cyrillvalentini/SAP-Extended/schematics/SAP-Extended/A-Register.kicad_sch

## KiCad design schematics/SAP-Extended/A-Register.kicad_sch (2023-11-03)

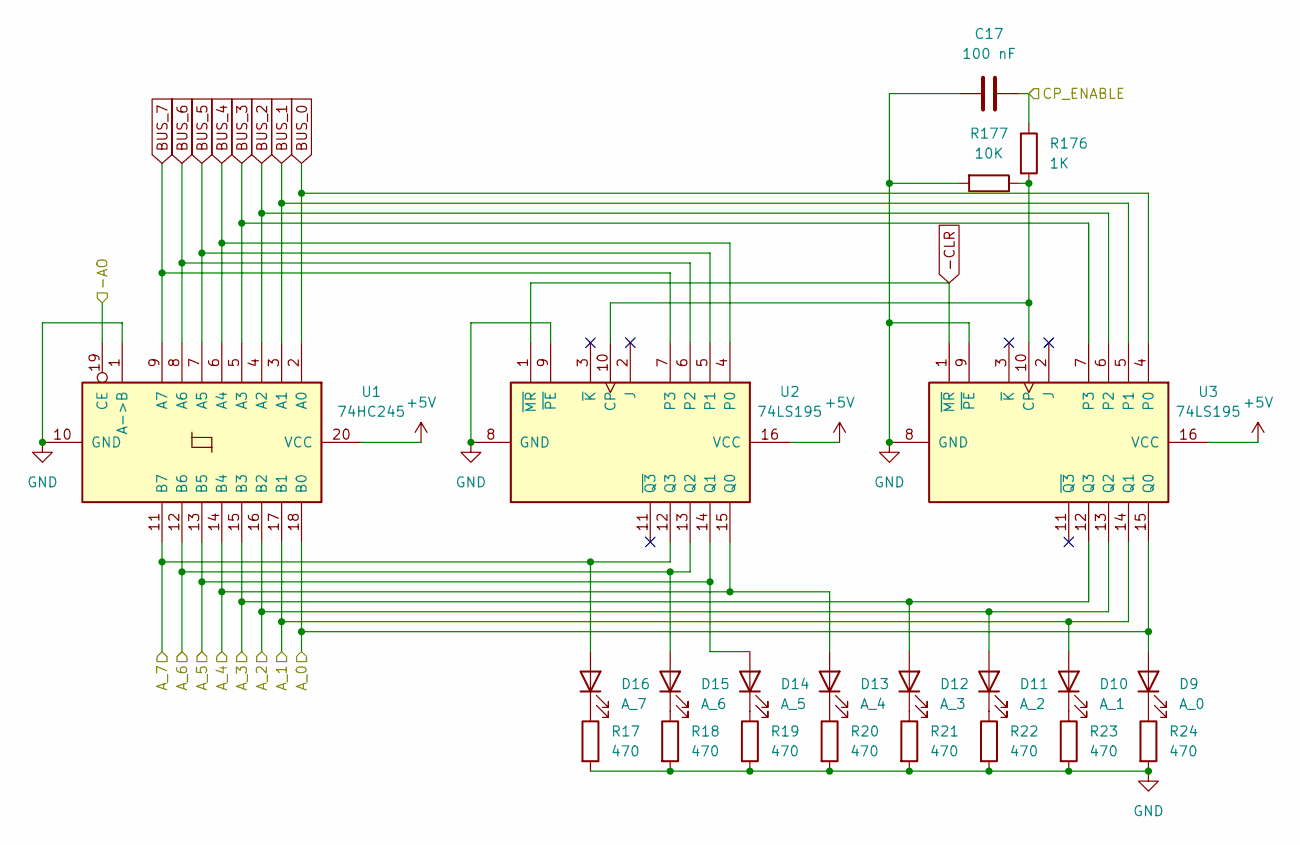
[picture p16: schematic A-Register.kicad_sch]

Parts:
C17: 100 nF; R_1206_3216Metric_Pad1.30x1.75mm_HandSolder
D9: A_0; LED_D3.0mm
D10: A_1; LED_D3.0mm
D11: A_2; LED_D3.0mm
D12: A_3; LED_D3.0mm
D13: A_4; LED_D3.0mm
D14: A_5; LED_D3.0mm
D15: A_6; LED_D3.0mm
D16: A_7; LED_D3.0mm
R17, R18, R19, R20, R21, R22, R23, R24: 470; R_1206_3216Metric_Pad1.30x1.75mm_HandSolder
R176: 1K; R_1206_3216Metric_Pad1.30x1.75mm_HandSolder
R177: 10K; R_1206_3216Metric_Pad1.30x1.75mm_HandSolder
U1: 74HC245; DIP-20_W7.62mm_Socket
U2, U3: 74LS195; DIP-16_W7.62mm_Socket

Connections:
+5V: U1.20 (VCC), U2.16 (VCC), U3.16 (VCC)
-AO: U1.19 (CE)
-CLR: U2.1 (~MR), U3.1 (~MR)
A_0: D9.2 (A), U1.18 (B0), U3.15 (Q0)
A_1: D10.2 (A), U1.17 (B1), U3.14 (Q1)
A_2: D11.2 (A), U1.16 (B2), U3.13 (Q2)
A_3: D12.2 (A), U1.15 (B3), U3.12 (Q3)
A_4: D13.2 (A), U1.14 (B4), U2.15 (Q0)
A_5: D14.2 (A), U1.13 (B5), U2.14 (Q1)
A_6: D15.2 (A), U1.12 (B6), U2.13 (Q2)
A_7: D16.2 (A), U1.11 (B7), U2.12 (Q3)
BUS_0: U1.2 (A0), U3.4 (P0)
BUS_1: U1.3 (A1), U3.5 (P1)
BUS_2: U1.4 (A2), U3.6 (P2)
BUS_3: U1.5 (A3), U3.7 (P3)
BUS_4: U1.6 (A4), U2.4 (P0)
BUS_5: U1.7 (A5), U2.5 (P1)
BUS_6: U1.8 (A6), U2.6 (P2)
BUS_7: U1.9 (A7), U2.7 (P3)
CP_ENABLE: C17.1, R176.1
GND: C17.2, R17.2, R18.2, R19.2, R20.2, R21.2, R22.2, R23.2, R24.2, R177.2, U1.1 (A->B), U1.10 (GND), U2.8 (GND), U2.9 (~PE), U3.8 (GND), U3.9 (~PE)
unnamed: D9.1 (K), R24.1
unnamed: D10.1 (K), R23.1
unnamed: D11.1 (K), R22.1
unnamed: D12.1 (K), R21.1
unnamed: D13.1 (K), R20.1
unnamed: D14.1 (K), R19.1
unnamed: D15.1 (K), R18.1
unnamed: D16.1 (K), R17.1
unnamed: R176.2, R177.1, U2.10 (CP), U3.10 (CP)
