cyrillvalentini/SAP-Extended/schematics/SAP-Extended/ALU.kicad_sch

## KiCad design schematics/SAP-Extended/ALU.kicad_sch (2023-11-03)

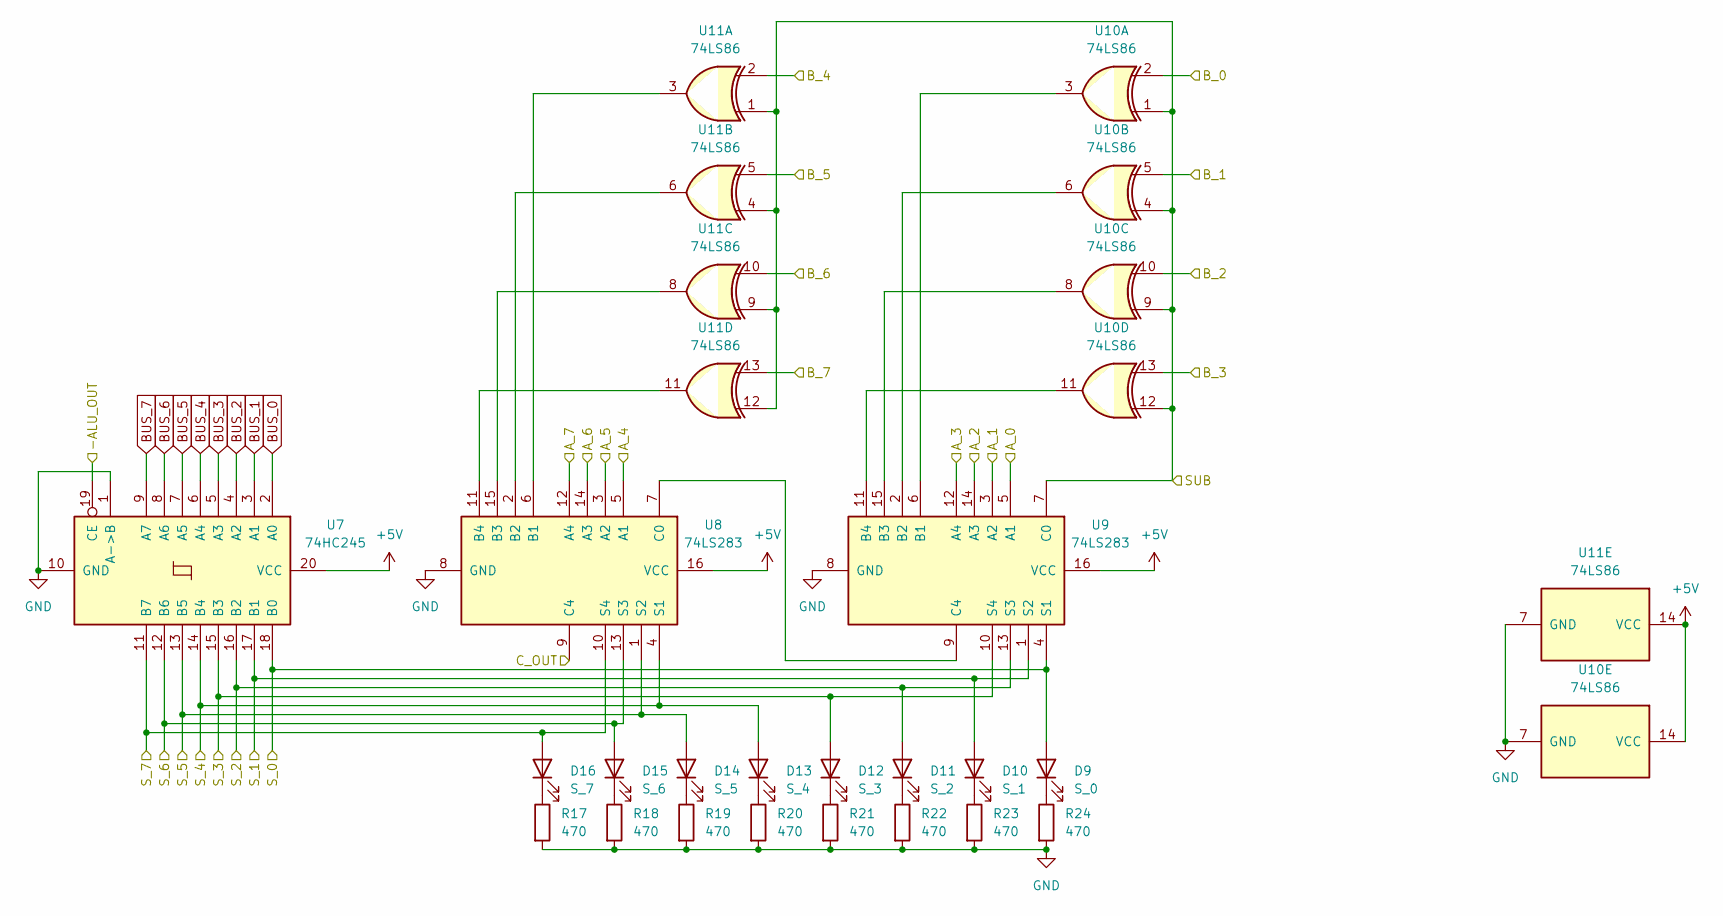
[picture p17: schematic ALU.kicad_sch]

Parts:
D9: S_0; LED_D3.0mm
D10: S_1; LED_D3.0mm
D11: S_2; LED_D3.0mm
D12: S_3; LED_D3.0mm
D13: S_4; LED_D3.0mm
D14: S_5; LED_D3.0mm
D15: S_6; LED_D3.0mm
D16: S_7; LED_D3.0mm
R17, R18, R19, R20, R21, R22, R23, R24: 470; R_1206_3216Metric_Pad1.30x1.75mm_HandSolder
U7: 74HC245; DIP-20_W7.62mm_Socket
U8, U9: 74LS283; DIP-16_W7.62mm_Socket
U10, U11: 74LS86; DIP-14_W7.62mm_Socket

Connections:
+5V: U7.20 (VCC), U8.16 (VCC), U9.16 (VCC), U10.14 (VCC), U11.14 (VCC)
-ALU_OUT: U7.19 (CE)
A_0: U9.5 (A1)
A_1: U9.3 (A2)
A_2: U9.14 (A3)
A_3: U9.12 (A4)
A_4: U8.5 (A1)
A_5: U8.3 (A2)
A_6: U8.14 (A3)
A_7: U8.12 (A4)
BUS_0: U7.2 (A0)
BUS_1: U7.3 (A1)
BUS_2: U7.4 (A2)
BUS_3: U7.5 (A3)
BUS_4: U7.6 (A4)
BUS_5: U7.7 (A5)
BUS_6: U7.8 (A6)
BUS_7: U7.9 (A7)
B_0: U10.2
B_1: U10.5
B_2: U10.10
B_3: U10.13
B_4: U11.2
B_5: U11.5
B_6: U11.10
B_7: U11.13
C_OUT: U8.9 (C4)
GND: R17.2, R18.2, R19.2, R20.2, R21.2, R22.2, R23.2, R24.2, U7.1 (A->B), U7.10 (GND), U8.8 (GND), U9.8 (GND), U10.7 (GND), U11.7 (GND)
unnamed: D9.1 (K), R24.1
unnamed: D10.1 (K), R23.1
unnamed: D11.1 (K), R22.1
unnamed: D12.1 (K), R21.1
unnamed: D13.1 (K), R20.1
unnamed: D14.1 (K), R19.1
unnamed: D15.1 (K), R18.1
unnamed: D16.1 (K), R17.1
unnamed: U8.7 (C0), U9.9 (C4)
unnamed: U9.6 (B1), U10.3
unnamed: U9.2 (B2), U10.6
unnamed: U9.15 (B3), U10.8
unnamed: U9.11 (B4), U10.11
unnamed: U8.6 (B1), U11.3
unnamed: U8.2 (B2), U11.6
unnamed: U8.15 (B3), U11.8
unnamed: U8.11 (B4), U11.11
SUB: U9.7 (C0), U10.1, U10.4, U10.9, U10.12, U11.1, U11.4, U11.9, U11.12
S_0: D9.2 (A), U7.18 (B0), U9.4 (S1)
S_1: D10.2 (A), U7.17 (B1), U9.1 (S2)
S_2: D11.2 (A), U7.16 (B2), U9.13 (S3)
S_3: D12.2 (A), U7.15 (B3), U9.10 (S4)
S_4: D13.2 (A), U7.14 (B4), U8.4 (S1)
S_5: D14.2 (A), U7.13 (B5), U8.1 (S2)
S_6: D15.2 (A), U7.12 (B6), U8.13 (S3)
S_7: D16.2 (A), U7.11 (B7), U8.10 (S4)
