cyrillvalentini/SAP-Extended/schematics/SAP-Extended/B-Register.kicad_sch

## KiCad design schematics/SAP-Extended/B-Register.kicad_sch (2023-11-03)

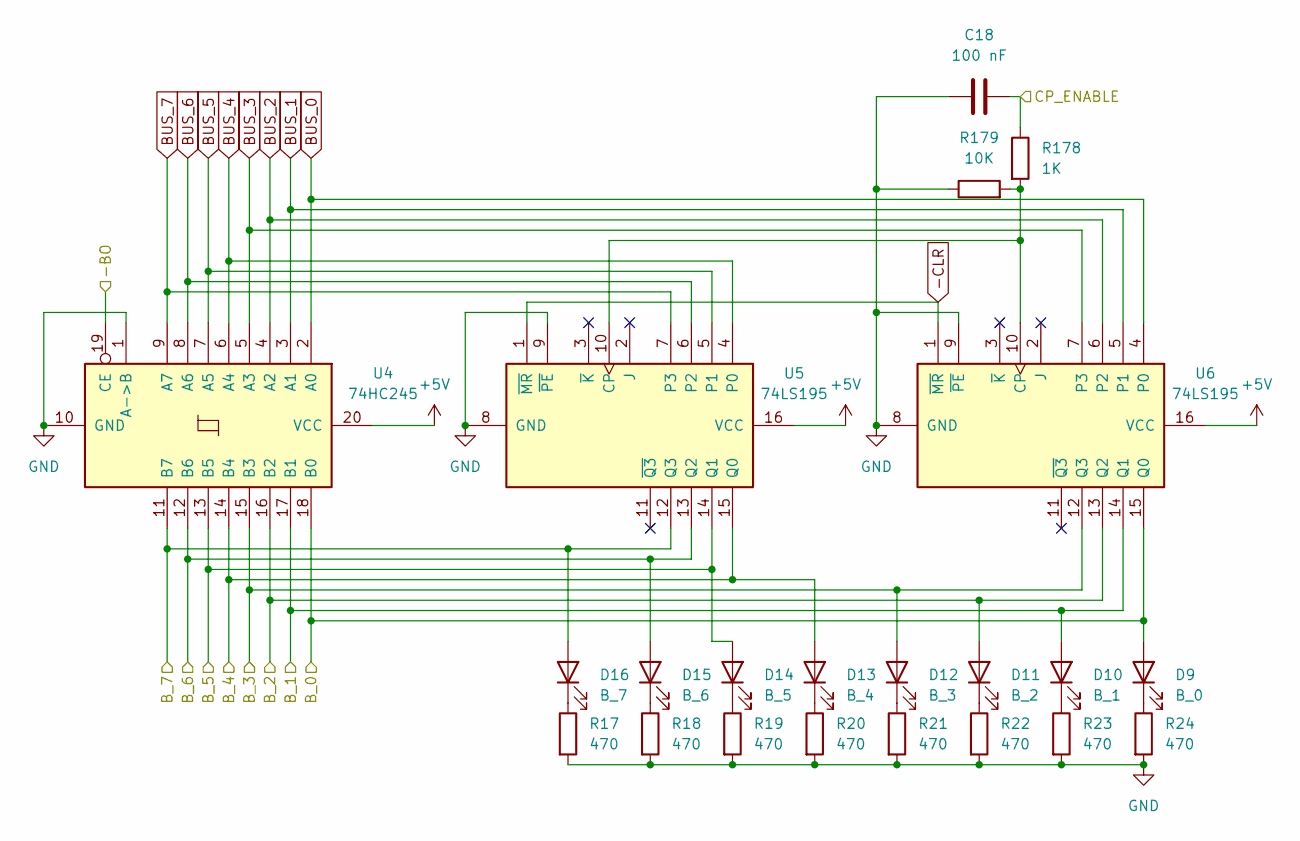
[picture p18: schematic B-Register.kicad_sch]

Parts:
C18: 100 nF
D9: B_0; LED_D3.0mm
D10: B_1; LED_D3.0mm
D11: B_2; LED_D3.0mm
D12: B_3; LED_D3.0mm
D13: B_4; LED_D3.0mm
D14: B_5; LED_D3.0mm
D15: B_6; LED_D3.0mm
D16: B_7; LED_D3.0mm
R17, R18, R19, R20, R21, R22, R23, R24: 470; R_1206_3216Metric_Pad1.30x1.75mm_HandSolder
R178: 1K; R_1206_3216Metric_Pad1.30x1.75mm_HandSolder
R179: 10K; R_1206_3216Metric_Pad1.30x1.75mm_HandSolder
U4: 74HC245; DIP-20_W7.62mm_Socket
U5, U6: 74LS195; DIP-16_W7.62mm_Socket

Connections:
+5V: U4.20 (VCC), U5.16 (VCC), U6.16 (VCC)
-BO: U4.19 (CE)
-CLR: U5.1 (~MR), U6.1 (~MR)
BUS_0: U4.2 (A0), U6.4 (P0)
BUS_1: U4.3 (A1), U6.5 (P1)
BUS_2: U4.4 (A2), U6.6 (P2)
BUS_3: U4.5 (A3), U6.7 (P3)
BUS_4: U4.6 (A4), U5.4 (P0)
BUS_5: U4.7 (A5), U5.5 (P1)
BUS_6: U4.8 (A6), U5.6 (P2)
BUS_7: U4.9 (A7), U5.7 (P3)
B_0: D9.2 (A), U4.18 (B0), U6.15 (Q0)
B_1: D10.2 (A), U4.17 (B1), U6.14 (Q1)
B_2: D11.2 (A), U4.16 (B2), U6.13 (Q2)
B_3: D12.2 (A), U4.15 (B3), U6.12 (Q3)
B_4: D13.2 (A), U4.14 (B4), U5.15 (Q0)
B_5: D14.2 (A), U4.13 (B5), U5.14 (Q1)
B_6: D15.2 (A), U4.12 (B6), U5.13 (Q2)
B_7: D16.2 (A), U4.11 (B7), U5.12 (Q3)
CP_ENABLE: C18.2, R178.1
GND: C18.1, R17.2, R18.2, R19.2, R20.2, R21.2, R22.2, R23.2, R24.2, R179.1, U4.1 (A->B), U4.10 (GND), U5.8 (GND), U5.9 (~PE), U6.8 (GND), U6.9 (~PE)
unnamed: D9.1 (K), R24.1
unnamed: D10.1 (K), R23.1
unnamed: D11.1 (K), R22.1
unnamed: D12.1 (K), R21.1
unnamed: D13.1 (K), R20.1
unnamed: D14.1 (K), R19.1
unnamed: D15.1 (K), R18.1
unnamed: D16.1 (K), R17.1
unnamed: R178.2, R179.2, U5.10 (CP), U6.10 (CP)
