cyrillvalentini/SAP-Extended/schematics/SAP-Extended/Clock.kicad_sch

## KiCad design schematics/SAP-Extended/Clock.kicad_sch (2023-11-03)

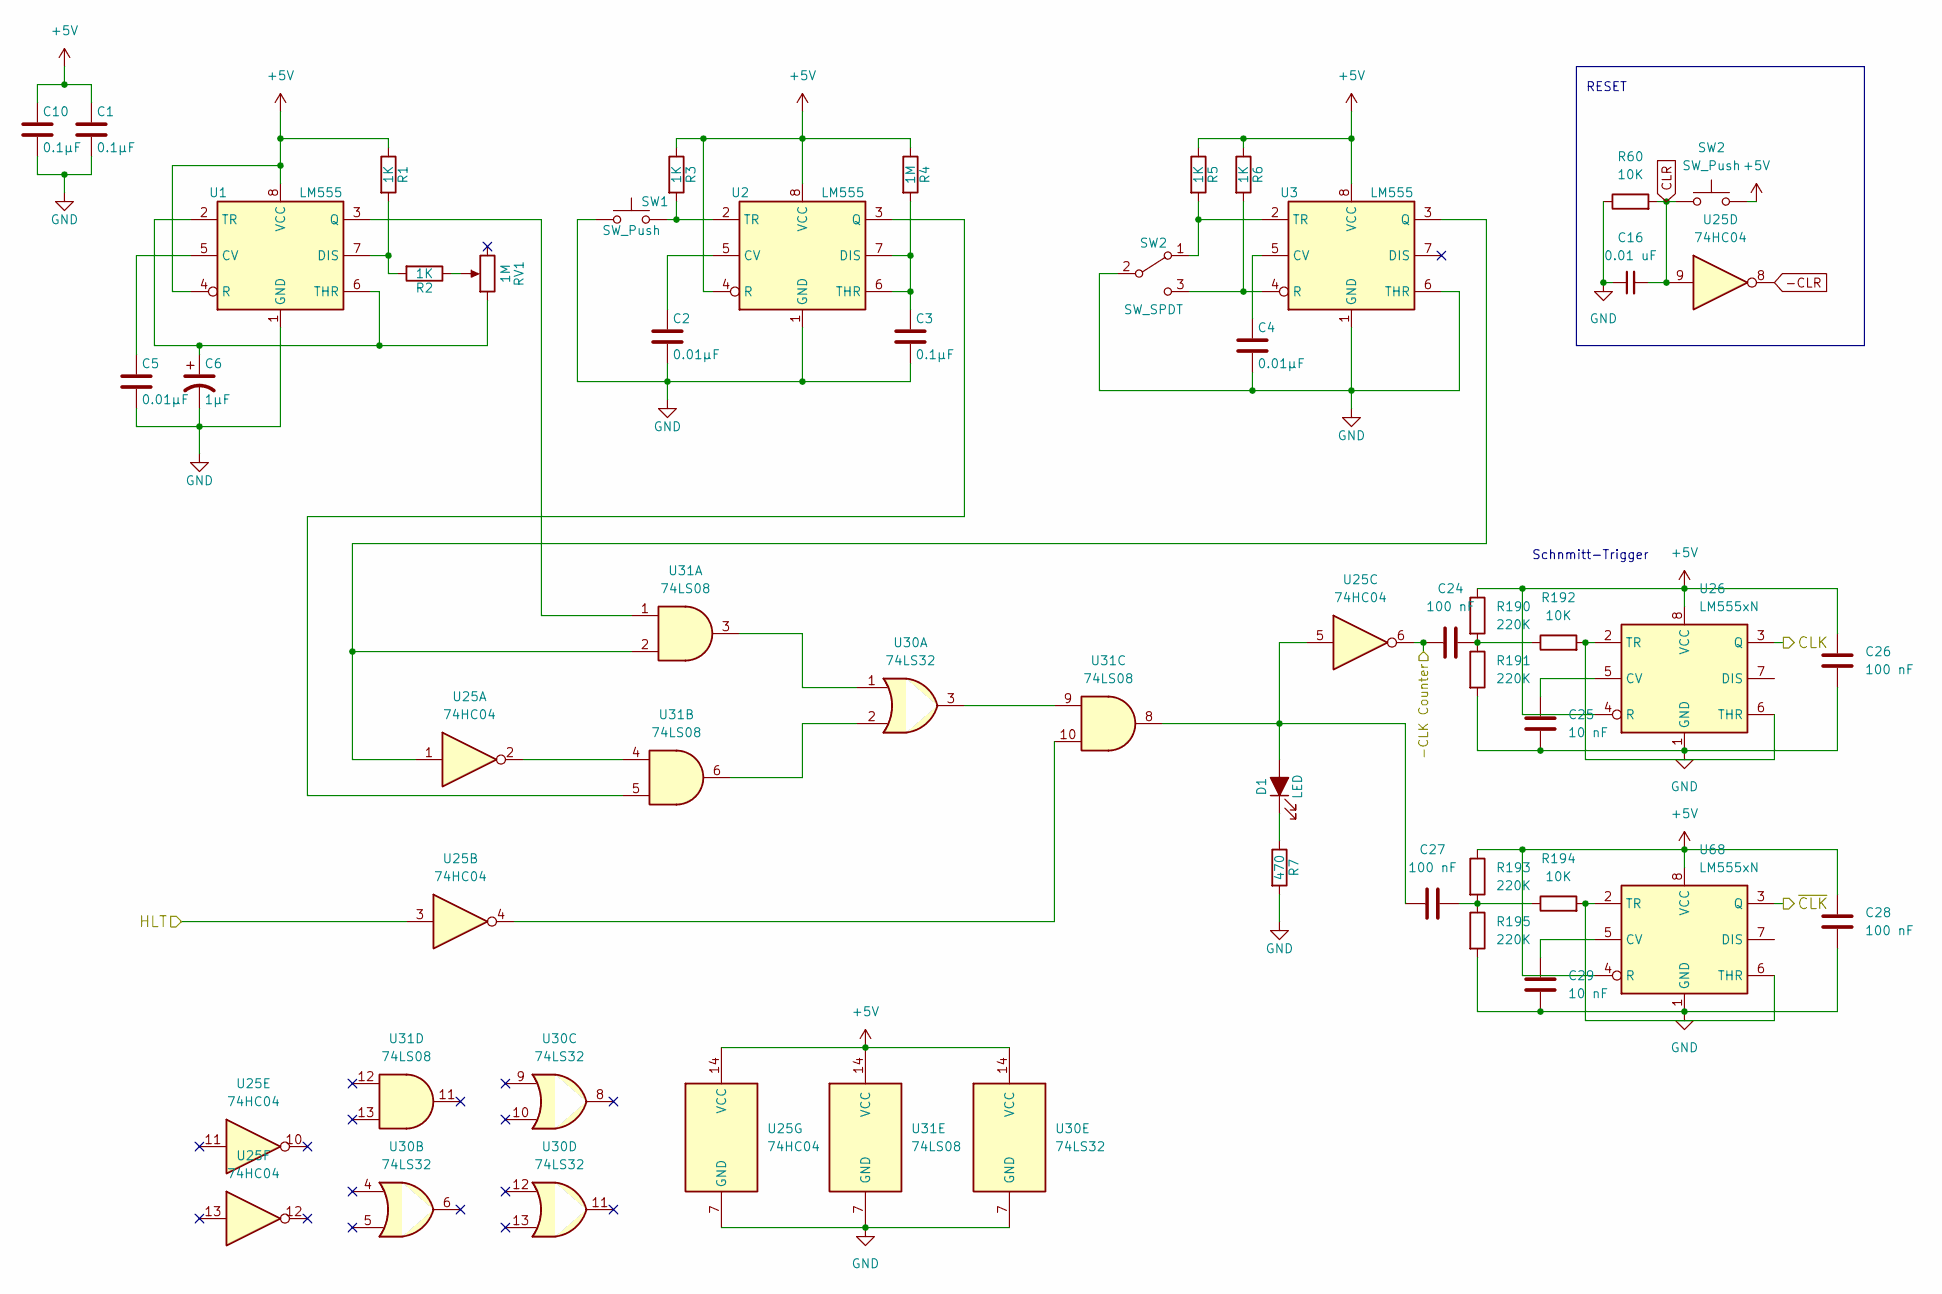
[picture p19: schematic Clock.kicad_sch]

Parts:
C1, C3, C10: 0.1µF; C_1206_3216Metric_Pad1.33x1.80mm_HandSolder
C2, C4, C5: 0.01µF; C_1206_3216Metric_Pad1.33x1.80mm_HandSolder
C6: 1µF; CP_Radial_D5.0mm_P2.00mm
C16: 0.01 uF; C_1206_3216Metric_Pad1.33x1.80mm_HandSolder
C24, C26, C27, C28: 100 nF; R_1206_3216Metric_Pad1.30x1.75mm_HandSolder
C25, C29: 10 nF; R_1206_3216Metric_Pad1.30x1.75mm_HandSolder
D1: LED; LED_D3.0mm
R1, R2, R3, R5, R6: 1K; R_1206_3216Metric_Pad1.30x1.75mm_HandSolder
R4: 1M; R_1206_3216Metric_Pad1.30x1.75mm_HandSolder
R7: 470; R_1206_3216Metric_Pad1.30x1.75mm_HandSolder
R60, R192, R194: 10K; R_1206_3216Metric_Pad1.30x1.75mm_HandSolder
R190, R191, R193, R195: 220K; R_1206_3216Metric_Pad1.30x1.75mm_HandSolder
RV1: 1M; Potentiometer_Bourns_PTV09A-1_Single_Vertical
SW1: SW_Push; SW_PUSH_6mm_H5mm
SW2: SW_Push; SW_PUSH_6mm
U1, U2, U3: LM555; DIP-8_W7.62mm_Socket
U25: 74HC04; DIP-14_W7.62mm_Socket
U26, U68: LM555xN; DIP-8_W7.62mm_Socket
U30: 74LS32; DIP-14_W7.62mm_Socket
U31: 74LS08; DIP-14_W7.62mm_Socket

Connections:
+5V: C1.1, C10.1, C26.1, C28.1, R1.1, R3.1, R4.1, R5.1, R6.1, R190.1, R193.1, SW2.2 (B), U1.4 (R), U1.8 (VCC), U2.4 (R), U2.8 (VCC), U3.8 (VCC), U25.14 (VCC), U26.4 (R), U26.8 (VCC), U30.14 (VCC), U31.14 (VCC), U68.4 (R), U68.8 (VCC)
-CLK Counter: C24.1, U25.6
-CLR: U25.8
CLK: U26.3 (Q)
CLR: C16.2, R60.2, SW2.1 (A), U25.9
GND: C1.2, C2.2, C3.2, C4.2, C5.2, C6.2, C10.2, C16.1, C25.2, C26.2, C28.2, C29.2, R7.2, R60.1, R191.2, R195.2, SW1.1, SW2.2 (B), U1.1 (GND), U2.1 (GND), U3.1 (GND), U3.6 (THR), U25.7 (GND), U26.1 (GND), U30.7 (GND), U31.7 (GND), U68.1 (GND)
HLT: U25.3
unnamed: C2.1, U2.5 (CV)
unnamed: C3.1, R4.2, U2.6 (THR), U2.7 (DIS)
unnamed: C4.1, U3.5 (CV)
unnamed: C5.1, U1.5 (CV)
unnamed: C6.1, RV1.1, U1.2 (TR), U1.6 (THR)
unnamed: C24.2, R190.2, R191.1, R192.1
unnamed: C25.1, U26.5 (CV)
unnamed: C27.1, D1.2 (A), U25.5, U31.8
unnamed: C27.2, R193.2, R194.1, R195.1
unnamed: C29.1, U68.5 (CV)
unnamed: D1.1 (K), R7.1
unnamed: R1.2, R2.2, U1.7 (DIS)
unnamed: R2.1, RV1.2
unnamed: R3.2, SW1.2, U2.2 (TR)
unnamed: R5.2, SW2.1 (A), U3.2 (TR)
unnamed: R6.2, SW2.3 (C), U3.4 (R)
unnamed: R192.2, U26.2 (TR), U26.6 (THR)
unnamed: R194.2, U68.2 (TR), U68.6 (THR)
unnamed: U1.3 (Q), U31.1
unnamed: U2.3 (Q), U31.5
unnamed: U3.3 (Q), U25.1, U31.2
unnamed: U25.2, U31.4
unnamed: U25.4, U31.10
unnamed: U30.1, U31.3
unnamed: U30.2, U31.6
unnamed: U30.3, U31.9
~CLK: U68.3 (Q)

Notes on the sheet:
Schnmitt-Trigger
RESET
