cyrillvalentini/SAP-Extended/schematics/SAP-Extended/Control Logic 1.kicad_sch

## KiCad design schematics/SAP-Extended/Control Logic 1.kicad_sch (2023-11-03)

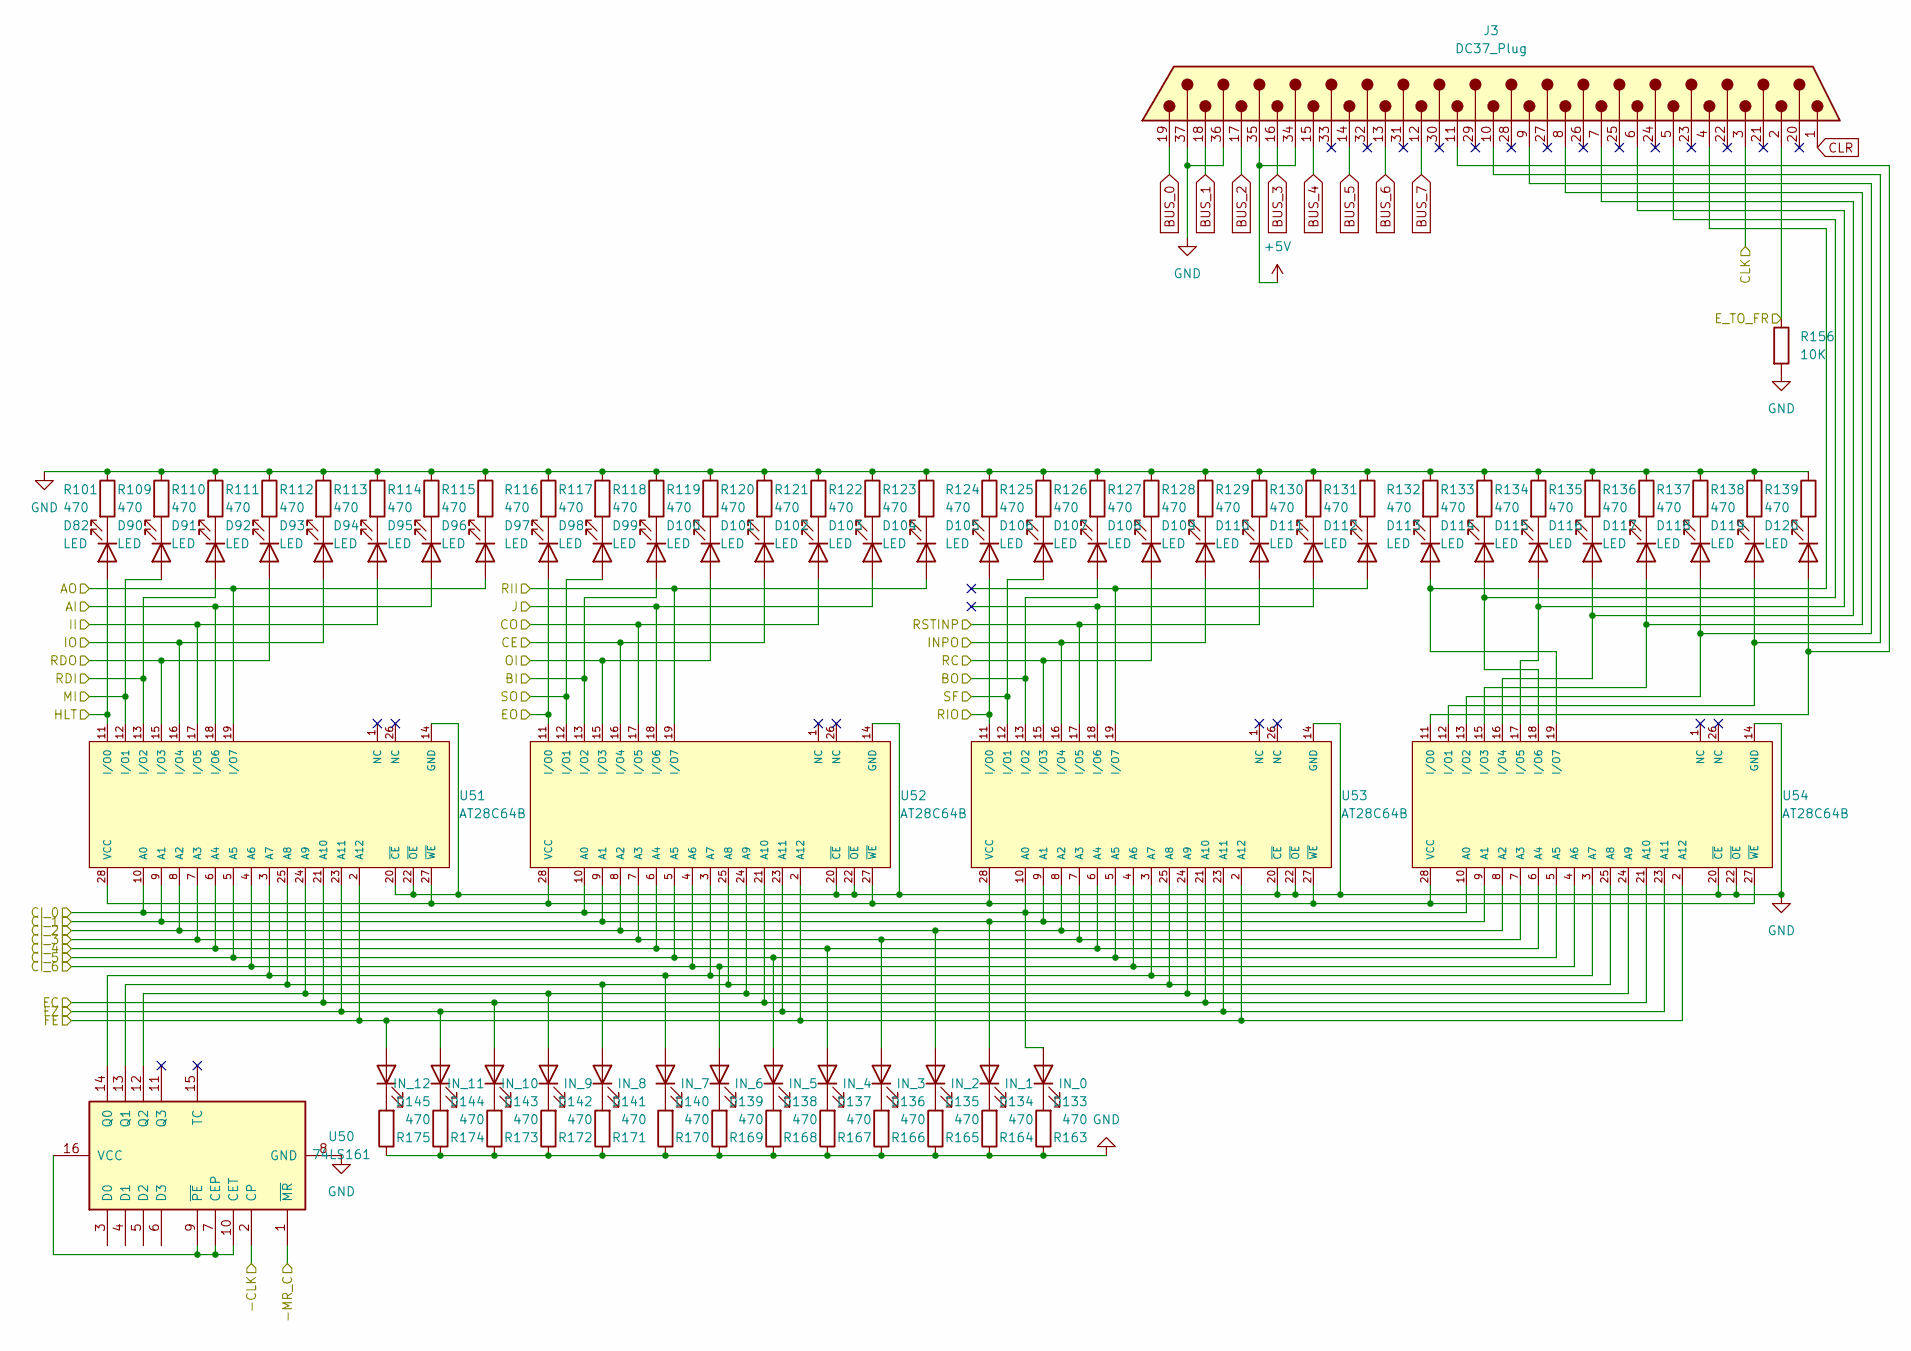
[picture p20: schematic Control Logic 1.kicad_sch]

Parts:
D82, D90, D91, D92, D93, D94, D95, D96, D97, D98, D99, D100, D101, D102, D103, D104, D105, D106, D107, D108, D109, D110, D111, D112, D113, D114, D115, D116, D117, D118, D119, D120: LED; LED_D3.0mm
D133: IN_0; LED_D3.0mm
D134: IN_1; LED_D3.0mm
D135: IN_2; LED_D3.0mm
D136: IN_3; LED_D3.0mm
D137: IN_4; LED_D3.0mm
D138: IN_5; LED_D3.0mm
D139: IN_6; LED_D3.0mm
D140: IN_7; LED_D3.0mm
D141: IN_8; LED_D3.0mm
D142: IN_9; LED_D3.0mm
D143: IN_10; LED_D3.0mm
D144: IN_11; LED_D3.0mm
D145: IN_12; LED_D3.0mm
J3: DC37_Plug; DSUB-37_Male_Horizontal_P2.77x2.84mm_EdgePinOffset4.94mm_Ho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
R101, R109, R110, R111, R112, R113, R114, R115, R116, R117, R118, R119, R120, R121, R122, R123, R124, R125, R126, R127, R128, R129, R130, R131, R132, R133, R134, R135, R136, R137, R138, R139, R163, R164, R165, R166, R167, R168, R169, R170, R171, R172, R173, R174, R175: 470; R_1206_3216Metric_Pad1.30x1.75mm_HandSolder
R156: 10K; R_1206_3216Metric_Pad1.30x1.75mm_HandSolder
U50: 74LS161; DIP-16_W7.62mm_Socket
U51, U52, U53, U54: AT28C64B; DIP-28_W15.24mm_Socket; Voltage - Supply 4.5V ~{} 5.5V; mouser part number 556-AT28C64B15PU; digikey description EEPROM Memory IC 64Kb (8K x 8) Parallel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

Connections:
+5V: J3.34, J3.35
-CLK: U50.2 (CP)
-MR_C: U50.1 (~MR)
AI: D95.2 (A), U51.18 (I/O6)
AO: D96.2 (A), U51.19 (I/O7)
BI: D99.2 (A), U52.13 (I/O2)
BO: D107.2 (A), U53.13 (I/O2)
BUS_0: J3.19
BUS_1: J3.18
BUS_2: J3.17
BUS_3: J3.16
BUS_4: J3.15
BUS_5: J3.14
BUS_6: J3.13
BUS_7: J3.12
CE: D101.2 (A), U52.16 (I/O4)
CI_0: D133.2 (A), U51.10 (A0), U52.10 (A0), U53.10 (A0), U54.10 (A0)
CI_1: D134.2 (A), U51.9 (A1), U52.9 (A1), U53.9 (A1), U54.9 (A1)
CI_2: D135.2 (A), U51.8 (A2), U52.8 (A2), U53.8 (A2), U54.8 (A2)
CI_3: D136.2 (A), U51.7 (A3), U52.7 (A3), U53.7 (A3), U54.7 (A3)
CI_4: D137.2 (A), U51.6 (A4), U52.6 (A4), U53.6 (A4), U54.6 (A4)
CI_5: D138.2 (A), U51.5 (A5), U52.5 (A5), U53.5 (A5), U54.5 (A5)
CI_6: D139.2 (A), U51.4 (A6), U52.4 (A6), U53.4 (A6), U54.4 (A6)
CLK: J3.3
CLR: J3.1
CO: D102.2 (A), U52.17 (I/O5)
EO: D97.2 (A), U52.11 (I/O0)
E_TO_FR: J3.2, R156.1
FC: D143.2 (A), U51.21 (A10), U52.21 (A10), U53.21 (A10), U54.21 (A10)
FE: D145.2 (A), U51.2 (A12), U52.2 (A12), U53.2 (A12), U54.2 (A12)
FZ: D144.2 (A), U51.23 (A11), U52.23 (A11), U53.23 (A11), U54.23 (A11)
GND: J3.36, J3.37, R101.1, R109.1, R110.1, R111.1, R112.1, R113.1, R114.1, R115.1, R116.1, R117.1, R118.1, R119.1, R120.1, R121.1, R122.1, R123.1, R124.1, R125.1, R126.1, R127.1, R128.1, R129.1, R130.1, R131.1, R132.1, R133.1, R134.1, R135.1, R136.1, R137.1, R138.1, R139.1, R156.2, R163.1, R164.1, R165.1, R166.1, R167.1, R168.1, R169.1, R170.1, R171.1, R172.1, R173.1, R174.1, R175.1, U50.8 (GND), U51.14 (GND), U51.20 (~CE), U51.22 (~OE), U52.14 (GND), U52.20 (~CE), U52.22 (~OE), U53.14 (GND), U53.20 (~CE), U53.22 (~OE), U54.14 (GND), U54.20 (~CE), U54.22 (~OE)
HLT: D82.2 (A), U51.11 (I/O0)
II: D94.2 (A), U51.17 (I/O5)
INPO: D109.2 (A), U53.16 (I/O4)
IO: D93.2 (A), U51.16 (I/O4)
J: D103.2 (A), U52.18 (I/O6)
MI: D90.2 (A), U51.12 (I/O1)
unnamed: D82.1 (K), R101.2
unnamed: D90.1 (K), R109.2
unnamed: D91.1 (K), R110.2
unnamed: D92.1 (K), R111.2
unnamed: D93.1 (K), R112.2
unnamed: D94.1 (K), R113.2
unnamed: D95.1 (K), R114.2
unnamed: D96.1 (K), R115.2
unnamed: D97.1 (K), R116.2
unnamed: D98.1 (K), R117.2
unnamed: D99.1 (K), R118.2
unnamed: D100.1 (K), R119.2
unnamed: D101.1 (K), R120.2
unnamed: D102.1 (K), R121.2
unnamed: D103.1 (K), R122.2
unnamed: D104.1 (K), R123.2
unnamed: D105.1 (K), R124.2
unnamed: D106.1 (K), R125.2
unnamed: D107.1 (K), R126.2
unnamed: D108.1 (K), R127.2
unnamed: D109.1 (K), R128.2
unnamed: D110.1 (K), R129.2
unnamed: D111.1 (K), R130.2
unnamed: D111.2 (A), U53.18 (I/O6)
unnamed: D112.1 (K), R131.2
unnamed: D112.2 (A), U53.19 (I/O7)
unnamed: D113.1 (K), R132.2
unnamed: D113.2 (A), J3.4, U54.19 (I/O7)
unnamed: D114.1 (K), R133.2
unnamed: D114.2 (A), J3.5, U54.18 (I/O6)
unnamed: D115.1 (K), R134.2
unnamed: D115.2 (A), J3.6, U54.17 (I/O5)
unnamed: D116.1 (K), R135.2
unnamed: D116.2 (A), J3.7, U54.16 (I/O4)
unnamed: D117.1 (K), R136.2
unnamed: D117.2 (A), J3.8, U54.15 (I/O3)
unnamed: D118.1 (K), R137.2
unnamed: D118.2 (A), J3.9, U54.13 (I/O2)
unnamed: D119.1 (K), R138.2
unnamed: D119.2 (A), J3.10, U54.12 (I/O1)
unnamed: D120.1 (K), R139.2
unnamed: D120.2 (A), J3.11, U54.11 (I/O0)
unnamed: D133.1 (K), R163.2
unnamed: D134.1 (K), R164.2
unnamed: D135.1 (K), R165.2
unnamed: D136.1 (K), R166.2
unnamed: D137.1 (K), R167.2
unnamed: D138.1 (K), R168.2
unnamed: D139.1 (K), R169.2
unnamed: D140.1 (K), R170.2
unnamed: D140.2 (A), U50.14 (Q0), U51.3 (A7), U52.3 (A7), U53.3 (A7), U54.3 (A7)
unnamed: D141.1 (K), R171.2
unnamed: D141.2 (A), U50.13 (Q1), U51.25 (A8), U52.25 (A8), U53.25 (A8), U54.25 (A8)
unnamed: D142.1 (K), R172.2
unnamed: D142.2 (A), U50.12 (Q2), U51.24 (A9), U52.24 (A9), U53.24 (A9), U54.24 (A9)
unnamed: D143.1 (K), R173.2
unnamed: D144.1 (K), R174.2
unnamed: D145.1 (K), R175.2
unnamed: U50.7 (CEP), U50.9 (~PE), U50.10 (CET), U50.16 (VCC)
unnamed: U51.27 (~WE), U51.28 (VCC), U52.27 (~WE), U52.28 (VCC), U53.27 (~WE), U53.28 (VCC), U54.27 (~WE), U54.28 (VCC)
OI: D100.2 (A), U52.15 (I/O3)
RC: D108.2 (A), U53.15 (I/O3)
RDI: D91.2 (A), U51.13 (I/O2)
RDO: D92.2 (A), U51.15 (I/O3)
RII: D104.2 (A), U52.19 (I/O7)
RIO: D105.2 (A), U53.11 (I/O0)
RSTINP: D110.2 (A), U53.17 (I/O5)
SF: D106.2 (A), U53.12 (I/O1)
SO: D98.2 (A), U52.12 (I/O1)
