cyrillvalentini/SAP-Extended/schematics/SAP-Extended/Control Logic 2.kicad_sch

## KiCad design schematics/SAP-Extended/Control Logic 2.kicad_sch (2023-11-03)

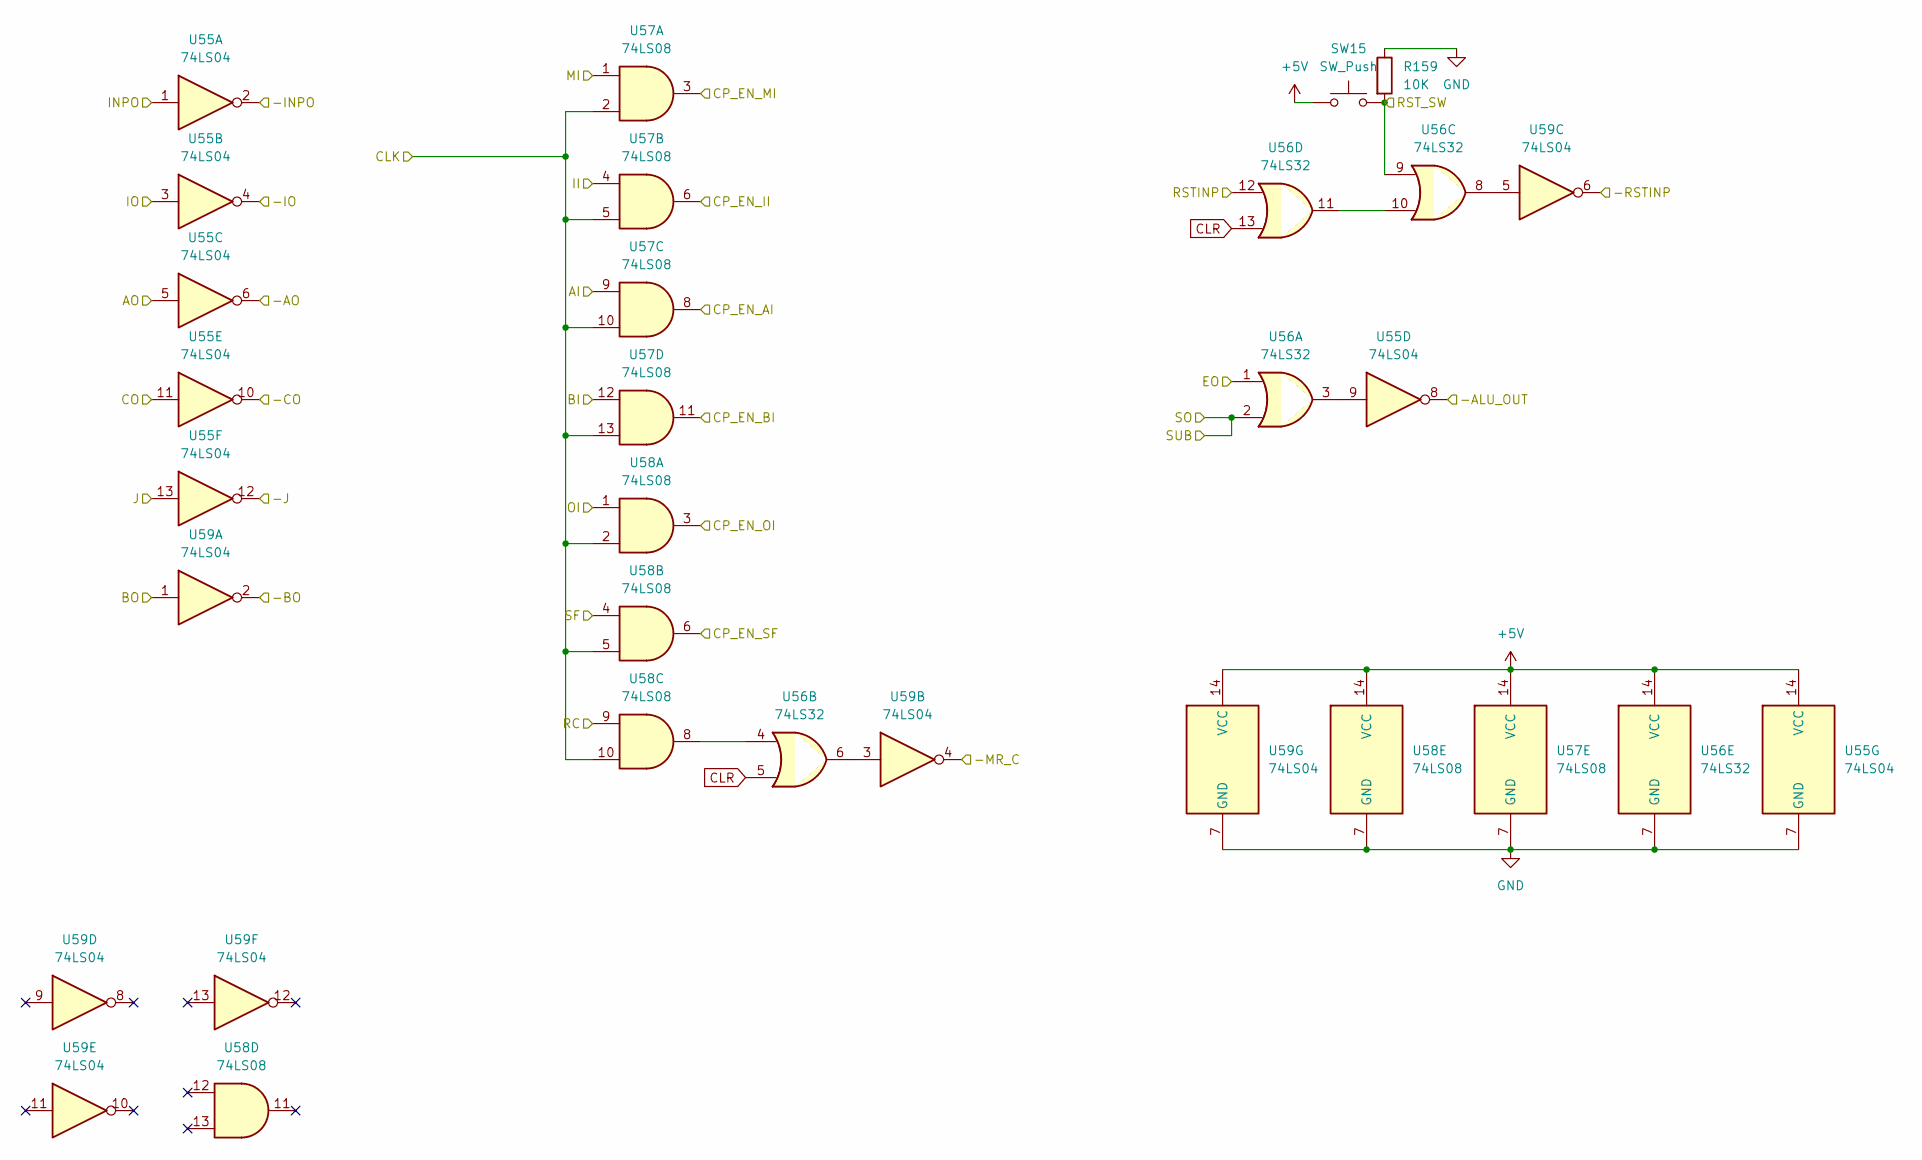
[picture p21: schematic Control Logic 2.kicad_sch]

Parts:
R159: 10K; R_1206_3216Metric_Pad1.30x1.75mm_HandSolder
SW15: SW_Push; SW_PUSH_6mm
U55, U59: 74LS04; DIP-14_W7.62mm_Socket
U56: 74LS32; DIP-14_W7.62mm_Socket
U57, U58: 74LS08; DIP-14_W7.62mm_Socket

Connections:
+5V: SW15.1, U55.14 (VCC), U56.14 (VCC), U57.14 (VCC), U58.14 (VCC), U59.14 (VCC)
-ALU_OUT: U55.8
-AO: U55.6
-BO: U59.2
-CO: U55.10
-INPO: U55.2
-IO: U55.4
-J: U55.12
-MR_C: U59.4
-RSTINP: U59.6
AI: U57.9
AO: U55.5
BI: U57.12
BO: U59.1
CLK: U57.2, U57.5, U57.10, U57.13, U58.2, U58.5, U58.10
CLR: U56.5, U56.13
CO: U55.11
CP_EN_AI: U57.8
CP_EN_BI: U57.11
CP_EN_II: U57.6
CP_EN_MI: U57.3
CP_EN_OI: U58.3
CP_EN_SF: U58.6
EO: U56.1
GND: R159.1, U55.7 (GND), U56.7 (GND), U57.7 (GND), U58.7 (GND), U59.7 (GND)
II: U57.4
INPO: U55.1
IO: U55.3
J: U55.13
MI: U57.1
unnamed: U55.9, U56.3
unnamed: U56.4, U58.8
unnamed: U56.6, U59.3
unnamed: U56.8, U59.5
unnamed: U56.10, U56.11
OI: U58.1
RC: U58.9
RSTINP: U56.12
RST_SW: R159.2, SW15.2, U56.9
SF: U58.4
SO: U56.2
