cyrillvalentini/SAP-Extended/schematics/SAP-Extended/Flags Register.kicad_sch

## KiCad design schematics/SAP-Extended/Flags Register.kicad_sch (2023-11-03)

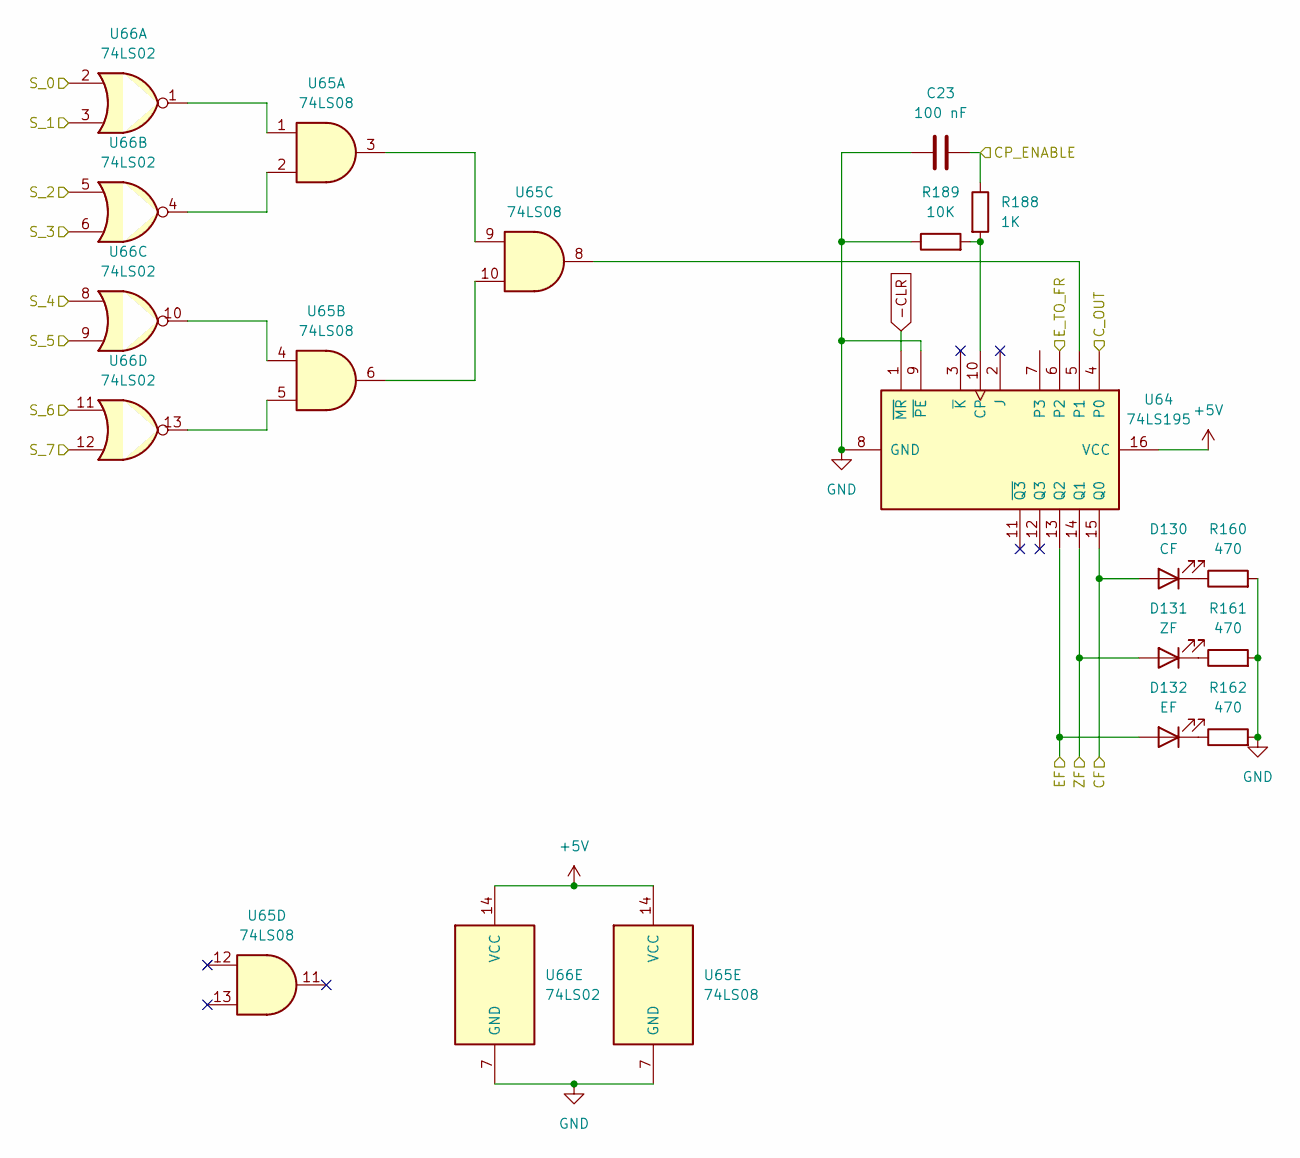
[picture p22: schematic Flags Register.kicad_sch]

Parts:
C23: 100 nF; R_1206_3216Metric_Pad1.30x1.75mm_HandSolder
D130: CF; LED_D3.0mm
D131: ZF; LED_D3.0mm
D132: EF; LED_D3.0mm
R160, R161, R162: 470; R_1206_3216Metric_Pad1.30x1.75mm_HandSolder
R188: 1K; R_1206_3216Metric_Pad1.30x1.75mm_HandSolder
R189: 10K; R_1206_3216Metric_Pad1.30x1.75mm_HandSolder
U64: 74LS195; DIP-16_W7.62mm_Socket
U65: 74LS08; DIP-14_W7.62mm_Socket
U66: 74LS02; DIP-14_W7.62mm_Socket

Connections:
+5V: U64.16 (VCC), U65.14 (VCC), U66.14 (VCC)
-CLR: U64.1 (~MR)
CF: D130.2 (A), U64.15 (Q0)
CP_ENABLE: C23.2, R188.1
C_OUT: U64.4 (P0)
EF: D132.2 (A), U64.13 (Q2)
E_TO_FR: U64.6 (P2)
GND: C23.1, R160.2, R161.2, R162.2, R189.1, U64.8 (GND), U64.9 (~PE), U65.7 (GND), U66.7 (GND)
unnamed: D130.1 (K), R160.1
unnamed: D131.1 (K), R161.1
unnamed: D132.1 (K), R162.1
unnamed: R188.2, R189.2, U64.10 (CP)
unnamed: U64.5 (P1), U65.8
unnamed: U65.1, U66.1
unnamed: U65.2, U66.4
unnamed: U65.3, U65.9
unnamed: U65.4, U66.10
unnamed: U65.5, U66.13
unnamed: U65.6, U65.10
S_0: U66.2
S_1: U66.3
S_2: U66.5
S_3: U66.6
S_4: U66.8
S_5: U66.9
S_6: U66.11
S_7: U66.12
ZF: D131.2 (A), U64.14 (Q1)
