cyrillvalentini/SAP-Extended/schematics/SAP-Extended/Input Register.kicad_sch

## KiCad design schematics/SAP-Extended/Input Register.kicad_sch (2023-11-03)

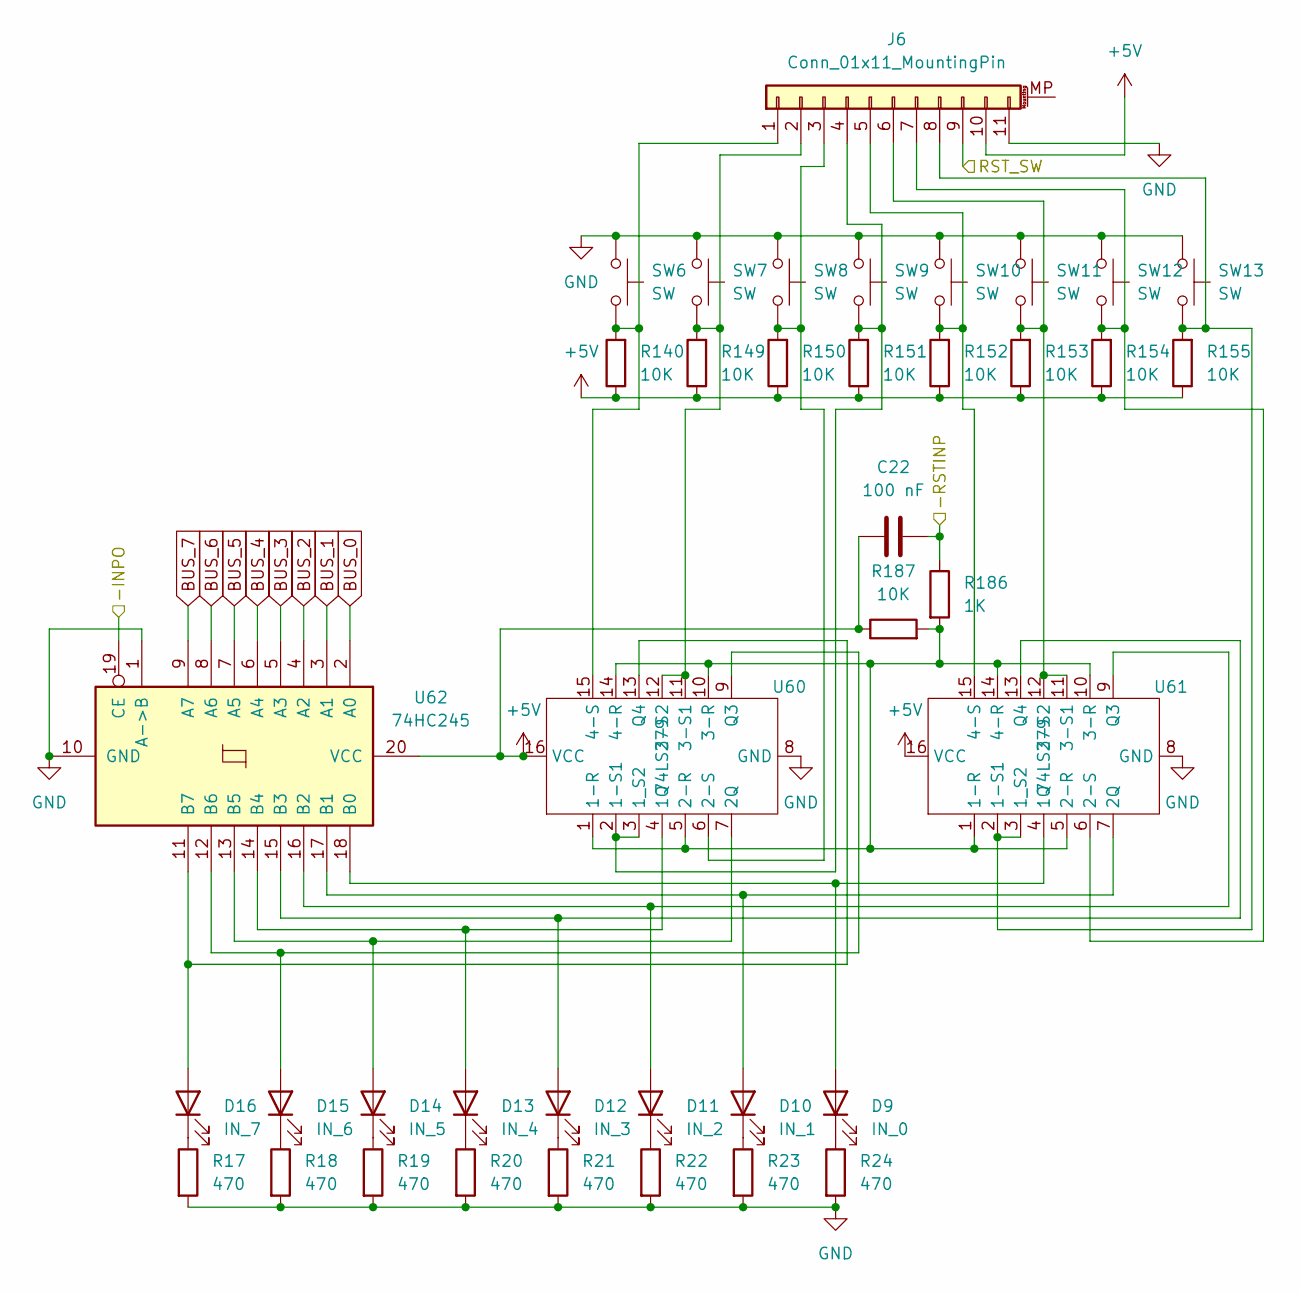
[picture p23: schematic Input Register.kicad_sch]

Parts:
C22: 100 nF; R_1206_3216Metric_Pad1.30x1.75mm_HandSolder
D9: IN_0; LED_D3.0mm
D10: IN_1; LED_D3.0mm
D11: IN_2; LED_D3.0mm
D12: IN_3; LED_D3.0mm
D13: IN_4; LED_D3.0mm
D14: IN_5; LED_D3.0mm
D15: IN_6; LED_D3.0mm
D16: IN_7; LED_D3.0mm
J6: Conn_01x11_MountingPin; PinHeader_1x11_P2.54mm_Vertical
R17, R18, R19, R20, R21, R22, R23, R24: 470; R_1206_3216Metric_Pad1.30x1.75mm_HandSolder
R140, R149, R150, R151, R152, R153, R154, R155, R187: 10K; R_1206_3216Metric_Pad1.30x1.75mm_HandSolder
R186: 1K; R_1206_3216Metric_Pad1.30x1.75mm_HandSolder
SW6, SW7, SW8, SW9, SW10, SW11, SW12, SW13: SW; SW_PUSH_6mm
U60, U61: 74LS279; DIP-16_W7.62mm_Socket
U62: 74HC245; DIP-20_W7.62mm_Socket

Connections:
+5V: C22.2, J6.10, R140.1, R149.1, R150.1, R151.1, R152.1, R153.1, R154.1, R155.1, R187.1, U60.16 (VCC), U61.16 (VCC), U62.20 (VCC)
-INPO: U62.19 (CE)
-RSTINP: C22.1, R186.1
BUS_0: U62.2 (A0)
BUS_1: U62.3 (A1)
BUS_2: U62.4 (A2)
BUS_3: U62.5 (A3)
BUS_4: U62.6 (A4)
BUS_5: U62.7 (A5)
BUS_6: U62.8 (A6)
BUS_7: U62.9 (A7)
GND: J6.11, R17.2, R18.2, R19.2, R20.2, R21.2, R22.2, R23.2, R24.2, SW6.1, SW7.1, SW8.1, SW9.1, SW10.1, SW11.1, SW12.1, SW13.1, U60.8 (GND), U61.8 (GND), U62.1 (A->B), U62.10 (GND)
unnamed: D9.1 (K), R24.1
unnamed: D9.2 (A), U61.4 (1Q), U62.18 (B0)
unnamed: D10.1 (K), R23.1
unnamed: D10.2 (A), U61.7 (2Q), U62.17 (B1)
unnamed: D11.1 (K), R22.1
unnamed: D11.2 (A), U61.9 (Q3), U62.16 (B2)
unnamed: D12.1 (K), R21.1
unnamed: D12.2 (A), U61.13 (Q4), U62.15 (B3)
unnamed: D13.1 (K), R20.1
unnamed: D13.2 (A), U60.4 (1Q), U62.14 (B4)
unnamed: D14.1 (K), R19.1
unnamed: D14.2 (A), U60.7 (2Q), U62.13 (B5)
unnamed: D15.1 (K), R18.1
unnamed: D15.2 (A), U60.9 (Q3), U62.12 (B6)
unnamed: D16.1 (K), R17.1
unnamed: D16.2 (A), U60.13 (Q4), U62.11 (B7)
unnamed: J6.1, R140.2, SW6.2, U60.15 (4-S)
unnamed: J6.2, R149.2, SW7.2, U60.11 (3-S1), U60.12 (3-S2)
unnamed: J6.3, R150.2, SW8.2, U60.6 (2-S)
unnamed: J6.4, R151.2, SW9.2, U60.2 (1-S1), U60.3 (1_S2)
unnamed: J6.5, R152.2, SW10.2, U61.15 (4-S)
unnamed: J6.6, R153.2, SW11.2, U61.11 (3-S1), U61.12 (3-S2)
unnamed: J6.7, R154.2, SW12.2, U61.6 (2-S)
unnamed: J6.8, R155.2, SW13.2, U61.2 (1-S1), U61.3 (1_S2)
unnamed: R186.2, R187.2, U60.1 (1-R), U60.5 (2-R), U60.10 (3-R), U60.14 (4-R), U61.1 (1-R), U61.5 (2-R), U61.10 (3-R), U61.14 (4-R)
RST_SW: J6.9
