cyrillvalentini/SAP-Extended/schematics/SAP-Extended/MAR.kicad_sch

## KiCad design schematics/SAP-Extended/MAR.kicad_sch (2023-11-03)

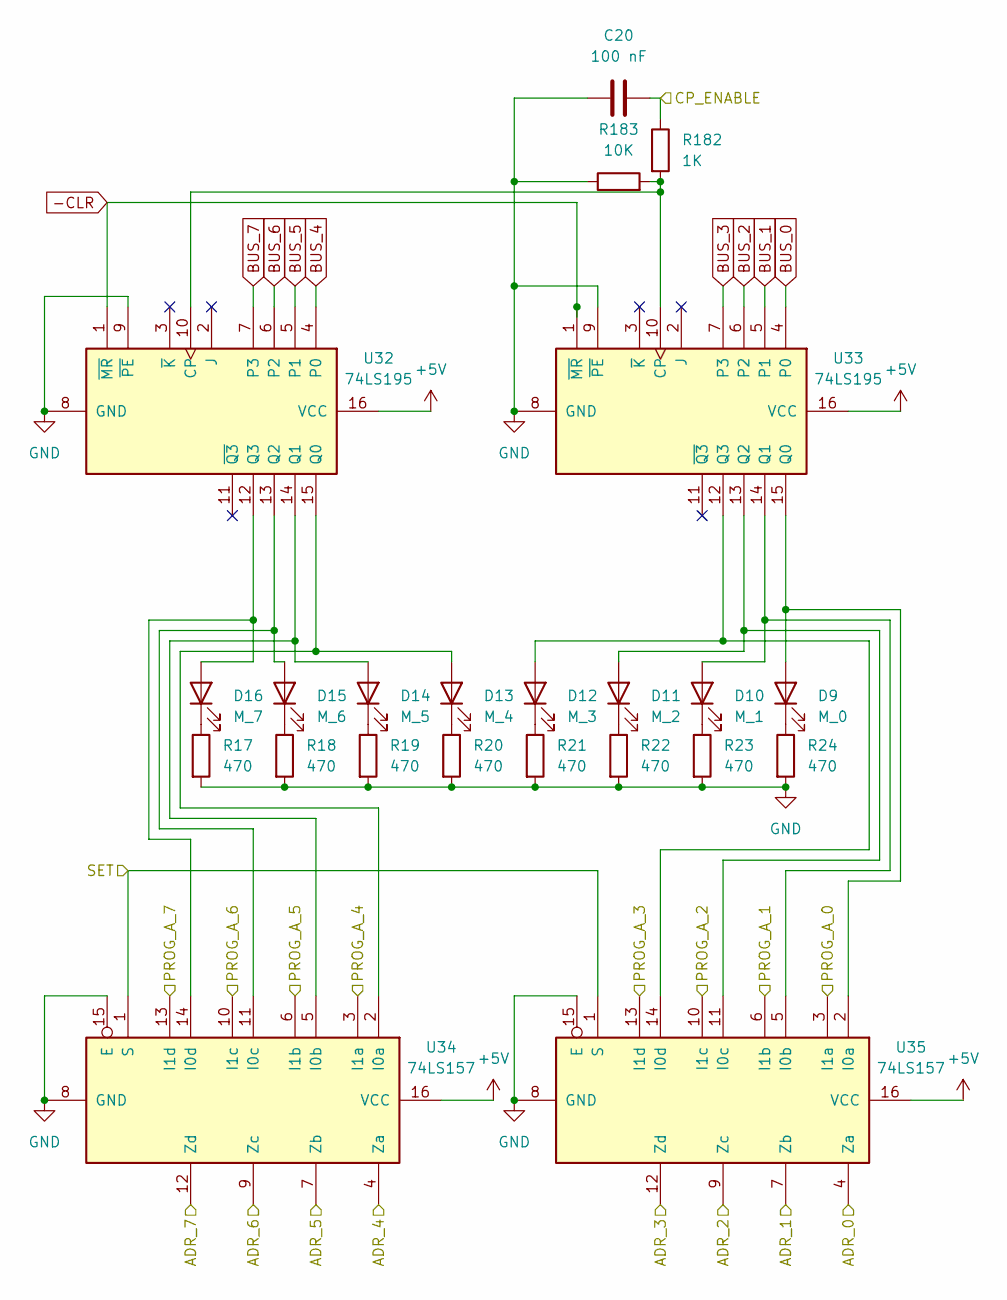
[picture p24: schematic MAR.kicad_sch]

Parts:
C20: 100 nF; R_1206_3216Metric_Pad1.30x1.75mm_HandSolder
D9: M_0; LED_D3.0mm
D10: M_1; LED_D3.0mm
D11: M_2; LED_D3.0mm
D12: M_3; LED_D3.0mm
D13: M_4; LED_D3.0mm
D14: M_5; LED_D3.0mm
D15: M_6; LED_D3.0mm
D16: M_7; LED_D3.0mm
R17, R18, R19, R20, R21, R22, R23, R24: 470; R_1206_3216Metric_Pad1.30x1.75mm_HandSolder
R182: 1K; R_1206_3216Metric_Pad1.30x1.75mm_HandSolder
R183: 10K; R_1206_3216Metric_Pad1.30x1.75mm_HandSolder
U32, U33: 74LS195; DIP-16_W7.62mm_Socket
U34, U35: 74LS157; DIP-16_W7.62mm_Socket

Connections:
+5V: U32.16 (VCC), U33.16 (VCC), U34.16 (VCC), U35.16 (VCC)
-CLR: U32.1 (~MR), U33.1 (~MR)
ADR_0: U35.4 (Za)
ADR_1: U35.7 (Zb)
ADR_2: U35.9 (Zc)
ADR_3: U35.12 (Zd)
ADR_4: U34.4 (Za)
ADR_5: U34.7 (Zb)
ADR_6: U34.9 (Zc)
ADR_7: U34.12 (Zd)
BUS_0: U33.4 (P0)
BUS_1: U33.5 (P1)
BUS_2: U33.6 (P2)
BUS_3: U33.7 (P3)
BUS_4: U32.4 (P0)
BUS_5: U32.5 (P1)
BUS_6: U32.6 (P2)
BUS_7: U32.7 (P3)
CP_ENABLE: C20.2, R182.1
GND: C20.1, R17.2, R18.2, R19.2, R20.2, R21.2, R22.2, R23.2, R24.2, R183.1, U32.8 (GND), U32.9 (~PE), U33.8 (GND), U33.9 (~PE), U34.8 (GND), U34.15 (E), U35.8 (GND), U35.15 (E)
unnamed: D9.1 (K), R24.1
unnamed: D9.2 (A), U33.15 (Q0), U35.2 (I0a)
unnamed: D10.1 (K), R23.1
unnamed: D10.2 (A), U33.14 (Q1), U35.5 (I0b)
unnamed: D11.1 (K), R22.1
unnamed: D11.2 (A), U33.13 (Q2), U35.11 (I0c)
unnamed: D12.1 (K), R21.1
unnamed: D12.2 (A), U33.12 (Q3), U35.14 (I0d)
unnamed: D13.1 (K), R20.1
unnamed: D13.2 (A), U32.15 (Q0), U34.2 (I0a)
unnamed: D14.1 (K), R19.1
unnamed: D14.2 (A), U32.14 (Q1), U34.5 (I0b)
unnamed: D15.1 (K), R18.1
unnamed: D15.2 (A), U32.13 (Q2), U34.11 (I0c)
unnamed: D16.1 (K), R17.1
unnamed: D16.2 (A), U32.12 (Q3), U34.14 (I0d)
unnamed: R182.2, R183.2, U32.10 (CP), U33.10 (CP)
PROG_A_0: U35.3 (I1a)
PROG_A_1: U35.6 (I1b)
PROG_A_2: U35.10 (I1c)
PROG_A_3: U35.13 (I1d)
PROG_A_4: U34.3 (I1a)
PROG_A_5: U34.6 (I1b)
PROG_A_6: U34.10 (I1c)
PROG_A_7: U34.13 (I1d)
SET: U34.1 (S), U35.1 (S)
