cyrillvalentini/SAP-Extended/schematics/SAP-Extended/Output-Register.kicad_sch

## KiCad design schematics/SAP-Extended/Output-Register.kicad_sch (2023-11-03)

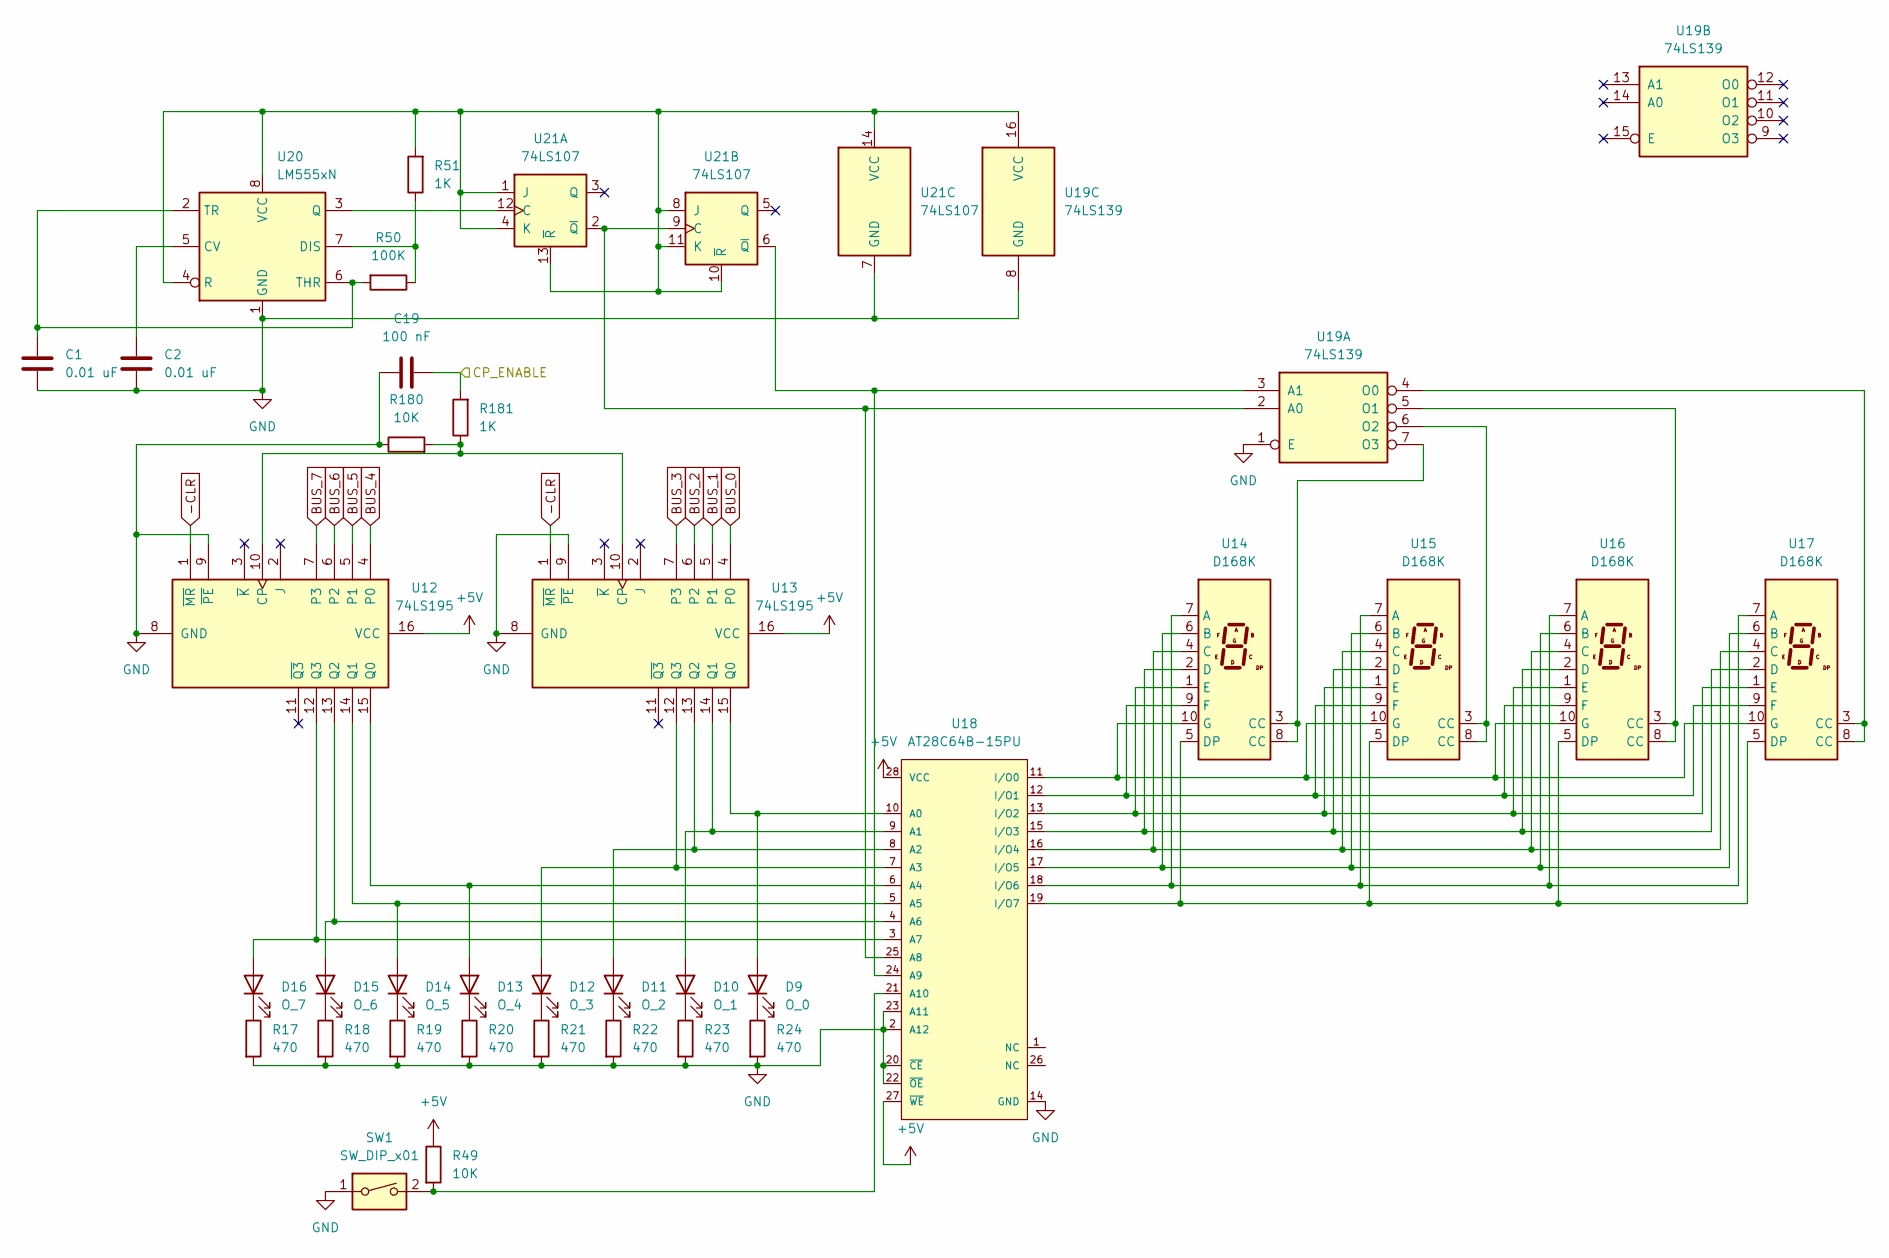
[picture p25: schematic Output-Register.kicad_sch]

Parts:
C1, C2: 0.01 uF; C_1206_3216Metric_Pad1.33x1.80mm_HandSolder
C19: 100 nF; R_1206_3216Metric_Pad1.30x1.75mm_HandSolder
D9: O_0; LED_D3.0mm
D10: O_1; LED_D3.0mm
D11: O_2; LED_D3.0mm
D12: O_3; LED_D3.0mm
D13: O_4; LED_D3.0mm
D14: O_5; LED_D3.0mm
D15: O_6; LED_D3.0mm
D16: O_7; LED_D3.0mm
R17, R18, R19, R20, R21, R22, R23, R24: 470; R_1206_3216Metric_Pad1.30x1.75mm_HandSolder
R49, R180: 10K; R_1206_3216Metric_Pad1.30x1.75mm_HandSolder
R50: 100K; R_1206_3216Metric_Pad1.30x1.75mm_HandSolder
R51, R181: 1K; R_1206_3216Metric_Pad1.30x1.75mm_HandSolder
SW1: SW_DIP_x01; SW_DIP_SPSTx01_Slide_9.78x4.72mm_W7.62mm_P2.54mm
U12, U13: 74LS195; DIP-16_W7.62mm_Socket
U14, U15, U16, U17: D168K; D1X8K
U18: AT28C64B-15PU; DIP-28_W15.24mm_Socket; Voltage - Supply 4.5V ~{} 5.5V; mouser part number 556-AT28C64B15PU; digikey description EEPROM Memory IC 64Kb (8K x 8) Parallel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
U19: 74LS139; DIP-16_W7.62mm_Socket
U20: LM555xN; DIP-8_W7.62mm_Socket
U21: 74LS107; DIP-14_W7.62mm_Socket

Connections:
+5V: R49.1, U12.16 (VCC), U13.16 (VCC), U18.27 (~WE), U18.28 (VCC)
-CLR: U12.1 (~MR), U13.1 (~MR)
BUS_0: U13.4 (P0)
BUS_1: U13.5 (P1)
BUS_2: U13.6 (P2)
BUS_3: U13.7 (P3)
BUS_4: U12.4 (P0)
BUS_5: U12.5 (P1)
BUS_6: U12.6 (P2)
BUS_7: U12.7 (P3)
CP_ENABLE: C19.2, R181.2
GND: C1.2, C2.2, C19.1, R17.2, R18.2, R19.2, R20.2, R21.2, R22.2, R23.2, R24.2, R180.1, SW1.1, U12.8 (GND), U12.9 (~PE), U13.8 (GND), U13.9 (~PE), U18.2 (A12), U18.14 (GND), U18.20 (~CE), U18.22 (~OE), U18.23 (A11), U19.1 (E), U19.8 (GND), U20.1 (GND), U21.7 (GND)
unnamed: C1.1, R50.2, U20.2 (TR), U20.6 (THR)
unnamed: C2.1, U20.5 (CV)
unnamed: D9.1 (K), R24.1
unnamed: D9.2 (A), U13.15 (Q0), U18.10 (A0)
unnamed: D10.1 (K), R23.1
unnamed: D10.2 (A), U13.14 (Q1), U18.9 (A1)
unnamed: D11.1 (K), R22.1
unnamed: D11.2 (A), U13.13 (Q2), U18.8 (A2)
unnamed: D12.1 (K), R21.1
unnamed: D12.2 (A), U13.12 (Q3), U18.7 (A3)
unnamed: D13.1 (K), R20.1
unnamed: D13.2 (A), U12.15 (Q0), U18.6 (A4)
unnamed: D14.1 (K), R19.1
unnamed: D14.2 (A), U12.14 (Q1), U18.5 (A5)
unnamed: D15.1 (K), R18.1
unnamed: D15.2 (A), U12.13 (Q2), U18.4 (A6)
unnamed: D16.1 (K), R17.1
unnamed: D16.2 (A), U12.12 (Q3), U18.3 (A7)
unnamed: R49.2, SW1.2, U18.21 (A10)
unnamed: R50.1, R51.1, U20.7 (DIS)
unnamed: R51.2, U19.16 (VCC), U20.4 (R), U20.8 (VCC), U21.1 (J), U21.4 (K), U21.8 (J), U21.10 (~R), U21.11 (K), U21.13 (~R), U21.14 (VCC)
unnamed: R180.2, R181.1, U12.10 (CP), U13.10 (CP)
unnamed: U14.1 (E), U15.1 (E), U16.1 (E), U17.1 (E), U18.13 (I/O2)
unnamed: U14.2 (D), U15.2 (D), U16.2 (D), U17.2 (D), U18.15 (I/O3)
unnamed: U14.3 (CC), U14.8 (CC), U19.7 (O3)
unnamed: U14.4 (C), U15.4 (C), U16.4 (C), U17.4 (C), U18.16 (I/O4)
unnamed: U14.5 (DP), U15.5 (DP), U16.5 (DP), U17.5 (DP), U18.19 (I/O7)
unnamed: U14.6 (B), U15.6 (B), U16.6 (B), U17.6 (B), U18.17 (I/O5)
unnamed: U14.7 (A), U15.7 (A), U16.7 (A), U17.7 (A), U18.18 (I/O6)
unnamed: U14.9 (F), U15.9 (F), U16.9 (F), U17.9 (F), U18.12 (I/O1)
unnamed: U14.10 (G), U15.10 (G), U16.10 (G), U17.10 (G), U18.11 (I/O0)
unnamed: U15.3 (CC), U15.8 (CC), U19.6 (O2)
unnamed: U16.3 (CC), U16.8 (CC), U19.5 (O1)
unnamed: U17.3 (CC), U17.8 (CC), U19.4 (O0)
unnamed: U18.24 (A9), U19.3 (A1), U21.6 (~Q)
unnamed: U18.25 (A8), U19.2 (A0), U21.2 (~Q), U21.9 (C)
unnamed: U20.3 (Q), U21.12 (C)
