cyrillvalentini/SAP-Extended/schematics/SAP-Extended/Power.kicad_sch

## KiCad design schematics/SAP-Extended/Power.kicad_sch (2023-11-03)

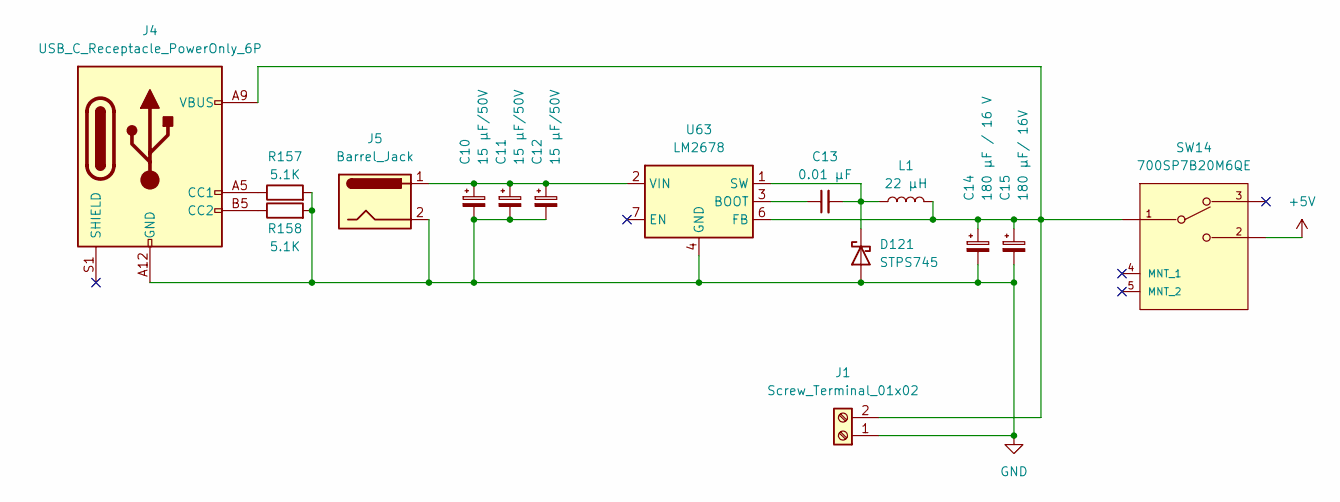
[picture p26: schematic Power.kicad_sch]

Parts:
C10, C11, C12: 15 µF/50V; CP_Radial_D5.0mm_P2.00mm
C13: 0.01 µF; C_1206_3216Metric
C14: 180 µF / 16 V; CP_Radial_D6.3mm_P2.50mm
C15: 180 µF/ 16V; CP_Radial_D6.3mm_P2.50mm
D121: STPS745; TO-220-2_Horizontal_TabDown
J1: Screw_Terminal_01x02; TerminalBlock_Phoenix_MKDS-1,5-2_1x02_P5.00mm_Horizontal
J4: USB_C_Receptacle_PowerOnly_6P; USB_C_Receptacle_GCT_USB4085
J5: Barrel_Jack; BarrelJack_GCT_DCJ200-10-A_Horizontal
L1: 22 µH; L_Radial_D12.0mm_P10.00mm_Neosid_SD12_style1
R157, R158: 5.1K; R_1206_3216Metric_Pad1.30x1.75mm_HandSolder
SW14: 700SP7B20M6QE; E-Switch-700SP7B20M6QE-0-0-MFG; voltage rating AC 250V; voltage rating DC 28V; mouser part number 612-700SP7B20M6QE; digikey description SWITCH PUSHBUTTON SPDT 3A 120V
U63: LM2678; TO-263-7_TabPin8

Connections:
+5V: SW14.2 (NO)
GND: C10.2, C11.2, C12.2, C14.2, C15.2, D121.2 (A), J1.1, J4.A12 (GND), J4.B12 (GND), J5.2, R157.2, R158.2, U63.4 (GND), U63.8 (GND)
unnamed: C10.1, C11.1, C12.1, J5.1, U63.2 (VIN)
unnamed: C13.1, U63.3 (BOOT)
unnamed: C13.2, D121.1 (K), L1.1, U63.1 (SW)
unnamed: C14.1, C15.1, J1.2, J4.A9 (VBUS), J4.B9 (VBUS), L1.2, SW14.1 (C), U63.6 (FB)
unnamed: J4.A5 (CC1), R157.1
unnamed: J4.B5 (CC2), R158.1
