cyrillvalentini/SAP-Extended/schematics/SAP-Extended/Program counter.kicad_sch

## KiCad design schematics/SAP-Extended/Program counter.kicad_sch (2023-11-03)

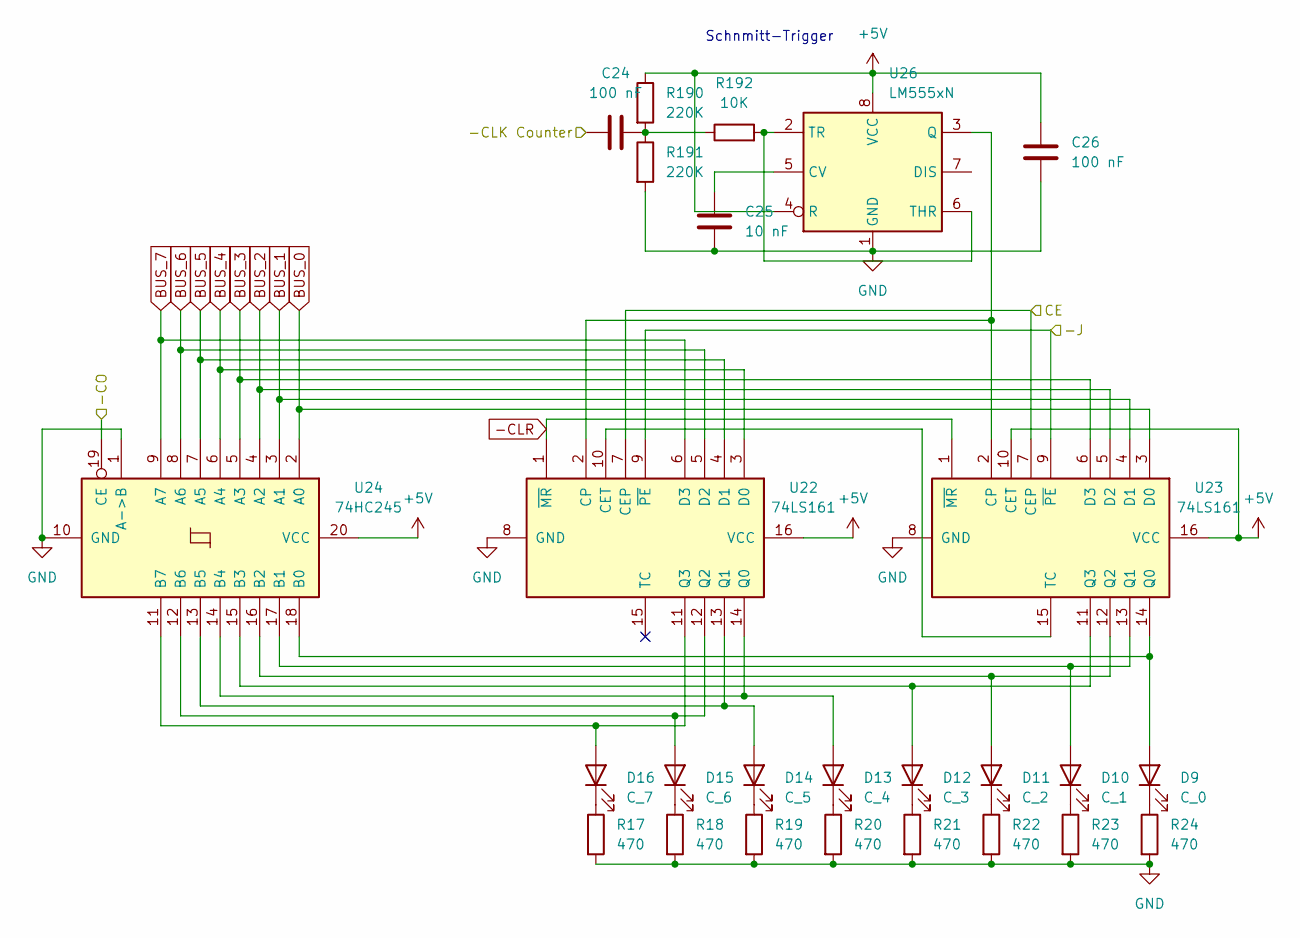
[picture p27: schematic Program counter.kicad_sch]

Parts:
C24, C26: 100 nF; R_1206_3216Metric_Pad1.30x1.75mm_HandSolder
C25: 10 nF; R_1206_3216Metric_Pad1.30x1.75mm_HandSolder
D9: C_0; LED_D3.0mm
D10: C_1; LED_D3.0mm
D11: C_2; LED_D3.0mm
D12: C_3; LED_D3.0mm
D13: C_4; LED_D3.0mm
D14: C_5; LED_D3.0mm
D15: C_6; LED_D3.0mm
D16: C_7; LED_D3.0mm
R17, R18, R19, R20, R21, R22, R23, R24: 470; R_1206_3216Metric_Pad1.30x1.75mm_HandSolder
R190, R191: 220K; R_1206_3216Metric_Pad1.30x1.75mm_HandSolder
R192: 10K; R_1206_3216Metric_Pad1.30x1.75mm_HandSolder
U22, U23: 74LS161; DIP-16_W7.62mm_Socket
U24: 74HC245; DIP-20_W7.62mm_Socket
U26: LM555xN; DIP-8_W7.62mm_Socket

Connections:
+5V: C26.1, R190.1, U22.16 (VCC), U23.10 (CET), U23.16 (VCC), U24.20 (VCC), U26.4 (R), U26.8 (VCC)
-CLK Counter: C24.1
-CLR: U22.1 (~MR), U23.1 (~MR)
-CO: U24.19 (CE)
-J: U22.9 (~PE), U23.9 (~PE)
BUS_0: U23.3 (D0), U24.2 (A0)
BUS_1: U23.4 (D1), U24.3 (A1)
BUS_2: U23.5 (D2), U24.4 (A2)
BUS_3: U23.6 (D3), U24.5 (A3)
BUS_4: U22.3 (D0), U24.6 (A4)
BUS_5: U22.4 (D1), U24.7 (A5)
BUS_6: U22.5 (D2), U24.8 (A6)
BUS_7: U22.6 (D3), U24.9 (A7)
CE: U22.7 (CEP), U23.7 (CEP)
GND: C25.2, C26.2, R17.2, R18.2, R19.2, R20.2, R21.2, R22.2, R23.2, R24.2, R191.2, U22.8 (GND), U23.8 (GND), U24.1 (A->B), U24.10 (GND), U26.1 (GND)
unnamed: C24.2, R190.2, R191.1, R192.1
unnamed: C25.1, U26.5 (CV)
unnamed: D9.1 (K), R24.1
unnamed: D9.2 (A), U23.14 (Q0), U24.18 (B0)
unnamed: D10.1 (K), R23.1
unnamed: D10.2 (A), U23.13 (Q1), U24.17 (B1)
unnamed: D11.1 (K), R22.1
unnamed: D11.2 (A), U23.12 (Q2), U24.16 (B2)
unnamed: D12.1 (K), R21.1
unnamed: D12.2 (A), U23.11 (Q3), U24.15 (B3)
unnamed: D13.1 (K), R20.1
unnamed: D13.2 (A), U22.14 (Q0), U24.14 (B4)
unnamed: D14.1 (K), R19.1
unnamed: D14.2 (A), U22.13 (Q1), U24.13 (B5)
unnamed: D15.1 (K), R18.1
unnamed: D15.2 (A), U22.12 (Q2), U24.12 (B6)
unnamed: D16.1 (K), R17.1
unnamed: D16.2 (A), U22.11 (Q3), U24.11 (B7)
unnamed: R192.2, U26.2 (TR), U26.6 (THR)
unnamed: U22.2 (CP), U23.2 (CP), U26.3 (Q)
unnamed: U22.10 (CET), U23.15 (TC)

Notes on the sheet:
Schnmitt-Trigger
