cyrillvalentini/SAP-Extended/schematics/SAP-Extended/Programmierport.kicad_sch

## KiCad design schematics/SAP-Extended/Programmierport.kicad_sch (2023-11-03)

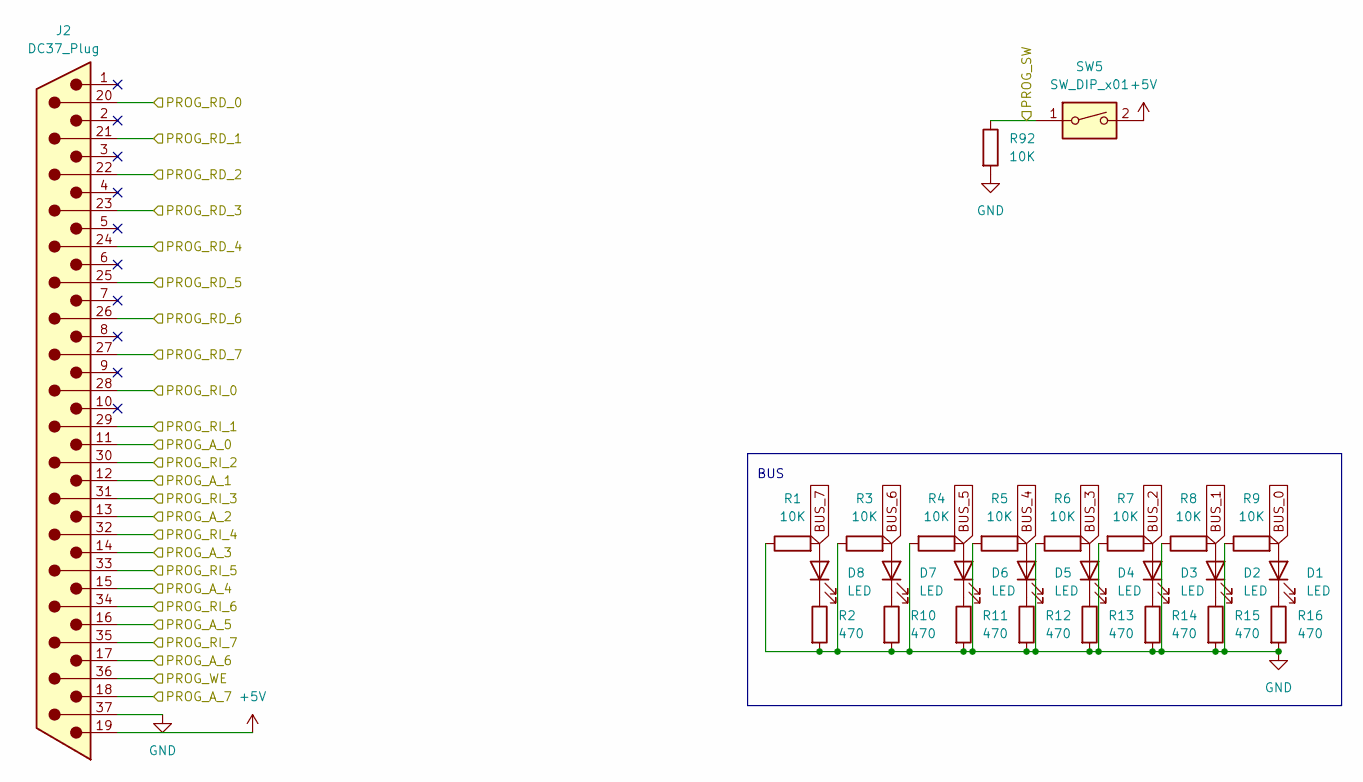
[picture p28: schematic Programmierport.kicad_sch]

Parts:
D1, D2, D3, D4, D5, D6, D7, D8: LED; LED_D3.0mm
J2: DC37_Plug; DSUB-37_Male_Horizontal_P2.77x2.84mm_EdgePinOffset4.94mm_Ho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
R1, R3, R4, R5, R6, R7, R8, R9, R92: 10K; R_1206_3216Metric_Pad1.30x1.75mm_HandSolder
R2, R10, R11, R12, R13, R14, R15, R16: 470; R_1206_3216Metric_Pad1.30x1.75mm_HandSolder
SW5: SW_DIP_x01; SW_DIP_SPSTx01_Slide_9.78x4.72mm_W7.62mm_P2.54mm

Connections:
+5V: J2.19, SW5.2
BUS_0: D1.2 (A), R9.2
BUS_1: D2.2 (A), R8.2
BUS_2: D3.2 (A), R7.1
BUS_3: D4.2 (A), R6.2
BUS_4: D5.2 (A), R5.1
BUS_5: D6.2 (A), R4.1
BUS_6: D7.2 (A), R3.2
BUS_7: D8.2 (A), R1.2
GND: J2.37, R1.1, R2.2, R3.1, R4.2, R5.2, R6.1, R7.2, R8.1, R9.1, R10.2, R11.2, R12.2, R13.2, R14.2, R15.2, R16.2, R92.2
unnamed: D1.1 (K), R16.1
unnamed: D2.1 (K), R15.1
unnamed: D3.1 (K), R14.1
unnamed: D4.1 (K), R13.1
unnamed: D5.1 (K), R12.1
unnamed: D6.1 (K), R11.1
unnamed: D7.1 (K), R10.1
unnamed: D8.1 (K), R2.1
PROG_A_0: J2.11
PROG_A_1: J2.12
PROG_A_2: J2.13
PROG_A_3: J2.14
PROG_A_4: J2.15
PROG_A_5: J2.16
PROG_A_6: J2.17
PROG_A_7: J2.18
PROG_RD_0: J2.20
PROG_RD_1: J2.21
PROG_RD_2: J2.22
PROG_RD_3: J2.23
PROG_RD_4: J2.24
PROG_RD_5: J2.25
PROG_RD_6: J2.26
PROG_RD_7: J2.27
PROG_RI_0: J2.28
PROG_RI_1: J2.29
PROG_RI_2: J2.30
PROG_RI_3: J2.31
PROG_RI_4: J2.32
PROG_RI_5: J2.33
PROG_RI_6: J2.34
PROG_RI_7: J2.35
PROG_SW: R92.1, SW5.1
PROG_WE: J2.36

Notes on the sheet:
BUS
