cyrillvalentini/SAP-Extended/schematics/SAP-Extended/RAM.kicad_sch

## KiCad design schematics/SAP-Extended/RAM.kicad_sch (2023-11-03)

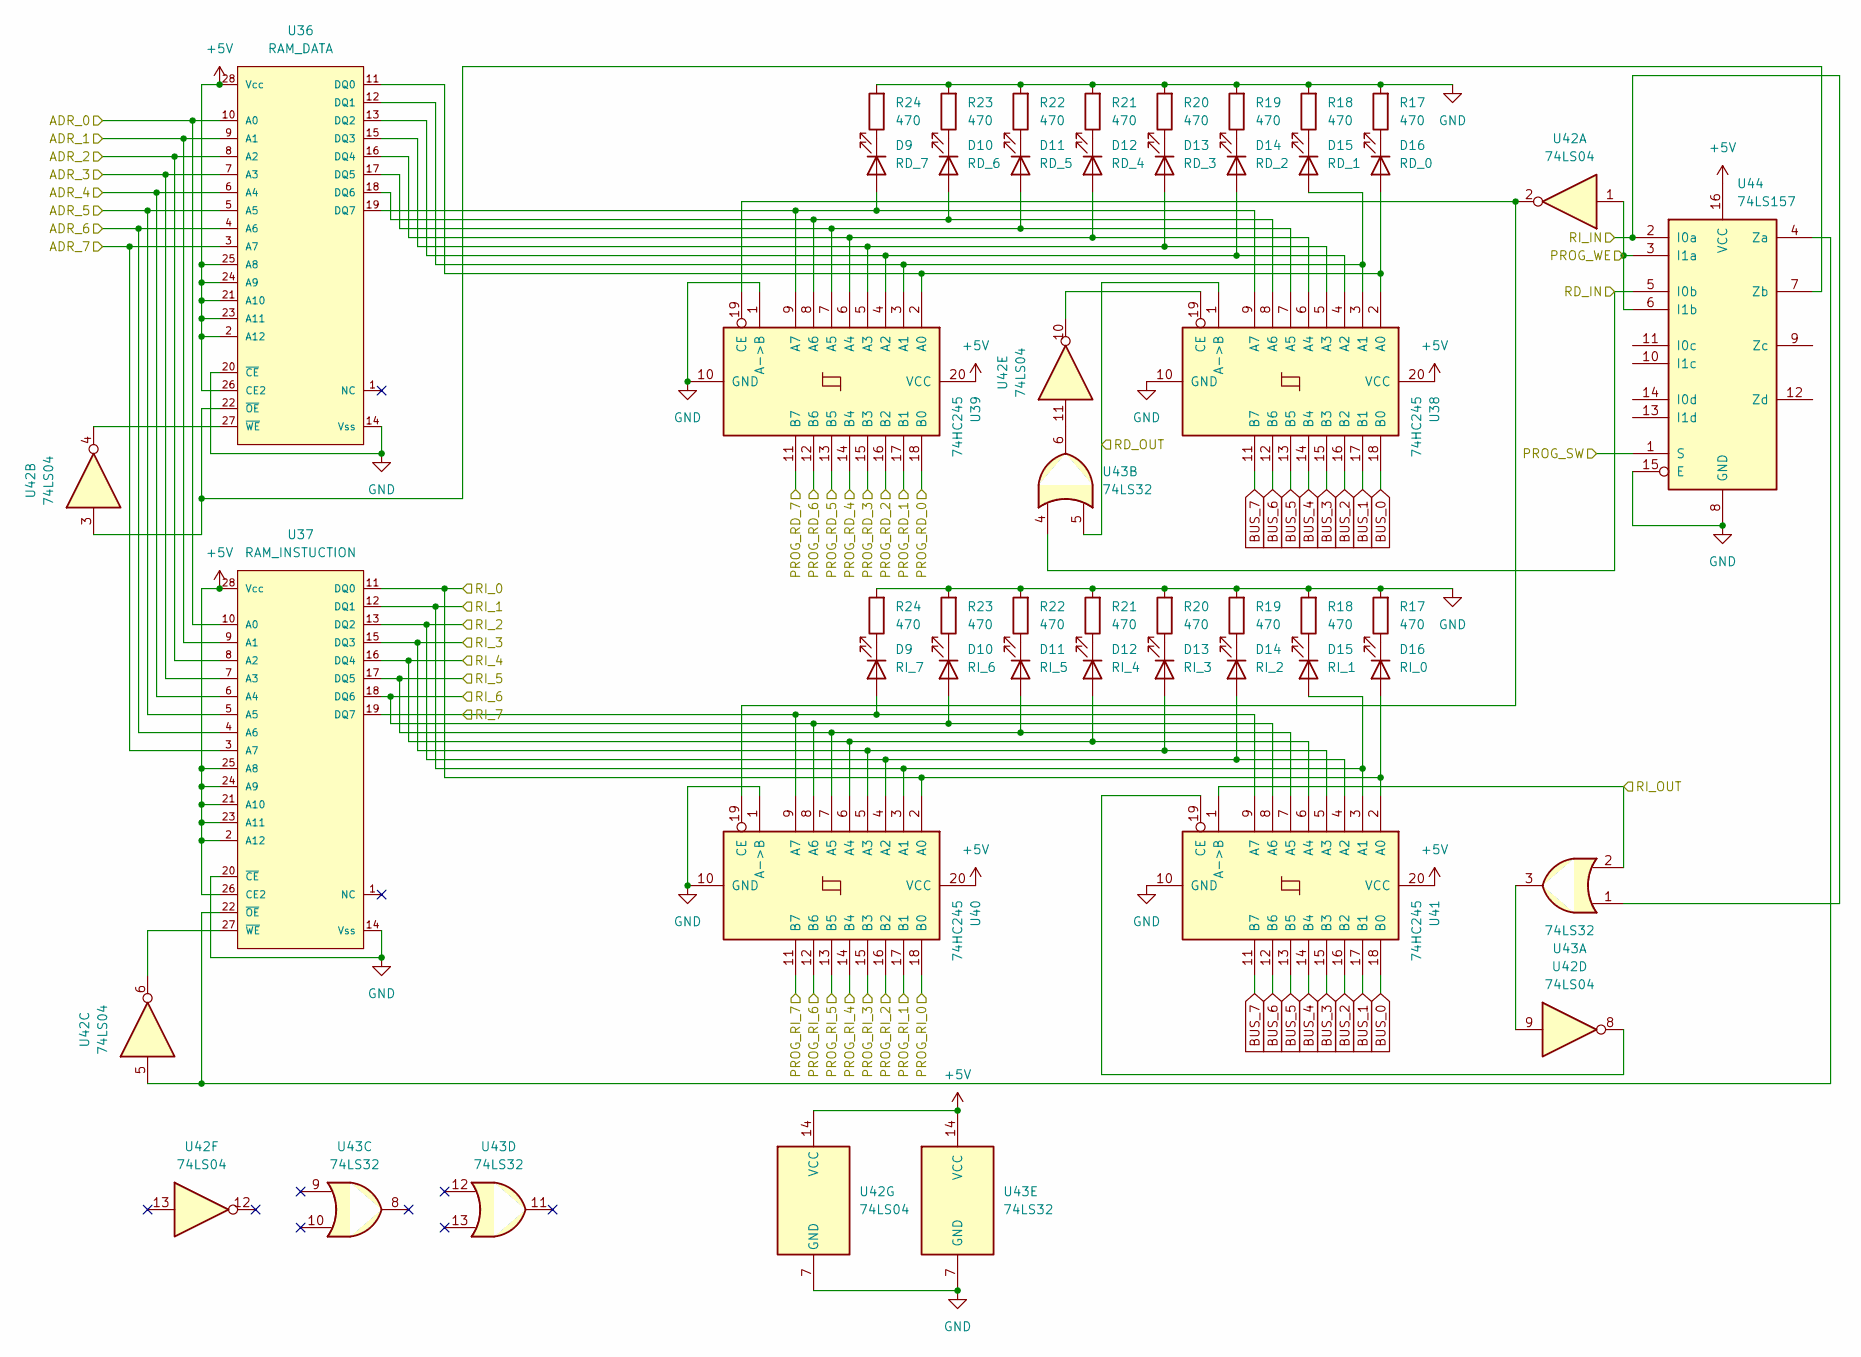
[picture p29: schematic RAM.kicad_sch]

Parts:
D9: RD_7; LED_D3.0mm
D10: RI_6; LED_D3.0mm
D11: RD_5; LED_D3.0mm
D12: RI_4; LED_D3.0mm
D13: RI_3; LED_D3.0mm
D14: RD_2; LED_D3.0mm
D15: RI_1; LED_D3.0mm
D16: RD_0; LED_D3.0mm
R17, R18, R19, R20, R21, R22, R23, R24: 470; R_1206_3216Metric_Pad1.30x1.75mm_HandSolder
U36: RAM_DATA; DIP-28_W15.24mm_Socket; mouser part number 913-AS6C6264-55PCN; digikey description IC SRAM 64K PARALLEL 28DIP
U37: RAM_INSTUCTION; DIP-28_W15.24mm_Socket; mouser part number 913-AS6C6264-55PCN; digikey description IC SRAM 64K PARALLEL 28DIP
U38, U39, U40, U41: 74HC245; DIP-20_W7.62mm_Socket
U42: 74LS04; DIP-14_W7.62mm_Socket
U43: 74LS32; DIP-14_W7.62mm_Socket
U44: 74LS157; DIP-16_W7.62mm_Socket

Connections:
+5V: U36.2 (A12), U36.21 (A10), U36.23 (A11), U36.24 (A9), U36.25 (A8), U36.26 (CE2), U36.28 (Vcc), U37.2 (A12), U37.21 (A10), U37.23 (A11), U37.24 (A9), U37.25 (A8), U37.26 (CE2), U37.28 (Vcc), U38.20 (VCC), U39.20 (VCC), U40.20 (VCC), U41.20 (VCC), U42.14 (VCC), U43.14 (VCC), U44.16 (VCC)
ADR_0: U36.10 (A0), U37.10 (A0)
ADR_1: U36.9 (A1), U37.9 (A1)
ADR_2: U36.8 (A2), U37.8 (A2)
ADR_3: U36.7 (A3), U37.7 (A3)
ADR_4: U36.6 (A4), U37.6 (A4)
ADR_5: U36.5 (A5), U37.5 (A5)
ADR_6: U36.4 (A6), U37.4 (A6)
ADR_7: U36.3 (A7), U37.3 (A7)
BUS_0: U38.18 (B0), U41.18 (B0)
BUS_1: U38.17 (B1), U41.17 (B1)
BUS_2: U38.16 (B2), U41.16 (B2)
BUS_3: U38.15 (B3), U41.15 (B3)
BUS_4: U38.14 (B4), U41.14 (B4)
BUS_5: U38.13 (B5), U41.13 (B5)
BUS_6: U38.12 (B6), U41.12 (B6)
BUS_7: U38.11 (B7), U41.11 (B7)
GND: R17.2, R18.2, R19.2, R20.2, R21.2, R22.2, R23.2, R24.2, U36.14 (Vss), U36.20 (~CE), U37.14 (Vss), U37.20 (~CE), U38.10 (GND), U39.1 (A->B), U39.10 (GND), U40.1 (A->B), U40.10 (GND), U41.10 (GND), U42.7 (GND), U43.7 (GND), U44.8 (GND), U44.15 (E)
unnamed: D9.1 (K), R24.1
unnamed: D9.2 (A), U36.19 (DQ7), U38.9 (A7), U39.9 (A7)
unnamed: D10.1 (K), R23.1
unnamed: D10.2 (A), U36.18 (DQ6), U38.8 (A6), U39.8 (A6)
unnamed: D11.1 (K), R22.1
unnamed: D11.2 (A), U36.17 (DQ5), U38.7 (A5), U39.7 (A5)
unnamed: D12.1 (K), R21.1
unnamed: D12.2 (A), U36.16 (DQ4), U38.6 (A4), U39.6 (A4)
unnamed: D13.1 (K), R20.1
unnamed: D13.2 (A), U36.15 (DQ3), U38.5 (A3), U39.5 (A3)
unnamed: D14.1 (K), R19.1
unnamed: D14.2 (A), U36.13 (DQ2), U38.4 (A2), U39.4 (A2)
unnamed: D15.1 (K), R18.1
unnamed: D15.2 (A), U36.12 (DQ1), U38.3 (A1), U39.3 (A1)
unnamed: D16.1 (K), R17.1
unnamed: D16.2 (A), U36.11 (DQ0), U38.2 (A0), U39.2 (A0)
unnamed: U36.22 (~OE), U42.3, U44.7 (Zb)
unnamed: U36.27 (~WE), U42.4
unnamed: U37.22 (~OE), U42.5, U44.4 (Za)
unnamed: U37.27 (~WE), U42.6
unnamed: U38.19 (CE), U42.10
unnamed: U39.19 (CE), U40.19 (CE), U42.2
unnamed: U41.19 (CE), U42.8
unnamed: U42.9, U43.3
unnamed: U42.11, U43.6
PROG_RD_0: U39.18 (B0)
PROG_RD_1: U39.17 (B1)
PROG_RD_2: U39.16 (B2)
PROG_RD_3: U39.15 (B3)
PROG_RD_4: U39.14 (B4)
PROG_RD_5: U39.13 (B5)
PROG_RD_6: U39.12 (B6)
PROG_RD_7: U39.11 (B7)
PROG_RI_0: U40.18 (B0)
PROG_RI_1: U40.17 (B1)
PROG_RI_2: U40.16 (B2)
PROG_RI_3: U40.15 (B3)
PROG_RI_4: U40.14 (B4)
PROG_RI_5: U40.13 (B5)
PROG_RI_6: U40.12 (B6)
PROG_RI_7: U40.11 (B7)
PROG_SW: U44.1 (S)
PROG_WE: U42.1, U44.3 (I1a), U44.6 (I1b)
RD_IN: U43.4, U44.5 (I0b)
RD_OUT: U38.1 (A->B), U43.5
RI_0: D16.2 (A), U37.11 (DQ0), U40.2 (A0), U41.2 (A0)
RI_1: D15.2 (A), U37.12 (DQ1), U40.3 (A1), U41.3 (A1)
RI_2: D14.2 (A), U37.13 (DQ2), U40.4 (A2), U41.4 (A2)
RI_3: D13.2 (A), U37.15 (DQ3), U40.5 (A3), U41.5 (A3)
RI_4: D12.2 (A), U37.16 (DQ4), U40.6 (A4), U41.6 (A4)
RI_5: D11.2 (A), U37.17 (DQ5), U40.7 (A5), U41.7 (A5)
RI_6: D10.2 (A), U37.18 (DQ6), U40.8 (A6), U41.8 (A6)
RI_7: D9.2 (A), U37.19 (DQ7), U40.9 (A7), U41.9 (A7)
RI_IN: U43.1, U44.2 (I0a)
RI_OUT: U41.1 (A->B), U43.2
