cyrillvalentini/SAP-Extended/schematics/SAP-Extended/untitled.kicad_sch

## KiCad design schematics/SAP-Extended/untitled.kicad_sch (2023-11-03)

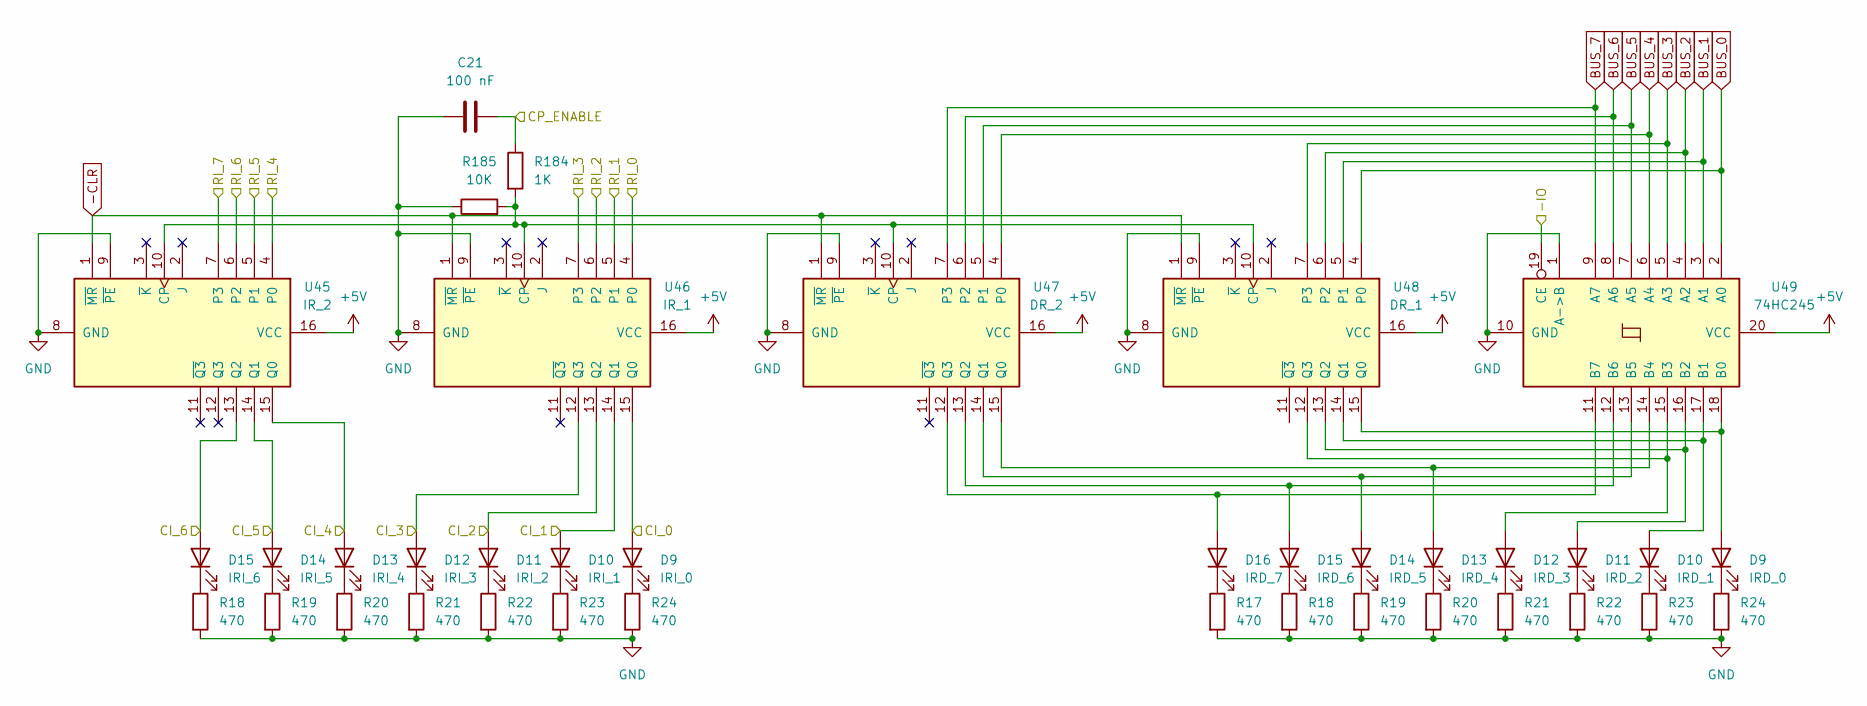
[picture p30: schematic untitled.kicad_sch]

Parts:
C21: 100 nF; R_1206_3216Metric_Pad1.30x1.75mm_HandSolder
D9: IRI_0; LED_D3.0mm
D10: IRI_1; LED_D3.0mm
D11: IRD_2; LED_D3.0mm
D12: IRD_3; LED_D3.0mm
D13: IRD_4; LED_D3.0mm
D14: IRD_5; LED_D3.0mm
D15: IRD_6; LED_D3.0mm
D16: IRD_7; LED_D3.0mm
R17, R18, R19, R20, R21, R22, R23, R24: 470; R_1206_3216Metric_Pad1.30x1.75mm_HandSolder
R184: 1K; R_1206_3216Metric_Pad1.30x1.75mm_HandSolder
R185: 10K; R_1206_3216Metric_Pad1.30x1.75mm_HandSolder
U45: IR_2; DIP-16_W7.62mm_Socket
U46: IR_1; DIP-16_W7.62mm_Socket
U47: DR_2; DIP-16_W7.62mm_Socket
U48: DR_1; DIP-16_W7.62mm_Socket
U49: 74HC245; DIP-20_W7.62mm_Socket

Connections:
+5V: U45.16 (VCC), U46.16 (VCC), U47.16 (VCC), U48.16 (VCC), U49.20 (VCC)
-CLR: U45.1 (~MR), U46.1 (~MR), U47.1 (~MR), U48.1 (~MR)
-IO: U49.19 (CE)
BUS_0: U48.4 (P0), U49.2 (A0)
BUS_1: U48.5 (P1), U49.3 (A1)
BUS_2: U48.6 (P2), U49.4 (A2)
BUS_3: U48.7 (P3), U49.5 (A3)
BUS_4: U47.4 (P0), U49.6 (A4)
BUS_5: U47.5 (P1), U49.7 (A5)
BUS_6: U47.6 (P2), U49.8 (A6)
BUS_7: U47.7 (P3), U49.9 (A7)
CI_0: D9.2 (A), U46.15 (Q0)
CI_1: D10.2 (A), U46.14 (Q1)
CI_2: D11.2 (A), U46.13 (Q2)
CI_3: D12.2 (A), U46.12 (Q3)
CI_4: D13.2 (A), U45.15 (Q0)
CI_5: D14.2 (A), U45.14 (Q1)
CI_6: D15.2 (A), U45.13 (Q2)
CP_ENABLE: C21.2, R184.1
GND: C21.1, R17.2, R18.2, R19.2, R20.2, R21.2, R22.2, R23.2, R24.2, R185.1, U45.8 (GND), U45.9 (~PE), U46.8 (GND), U46.9 (~PE), U47.8 (GND), U47.9 (~PE), U48.8 (GND), U48.9 (~PE), U49.1 (A->B), U49.10 (GND)
unnamed: D9.1 (K), R24.1
unnamed: D9.2 (A), U48.15 (Q0), U49.18 (B0)
unnamed: D10.1 (K), R23.1
unnamed: D10.2 (A), U48.14 (Q1), U49.17 (B1)
unnamed: D11.1 (K), R22.1
unnamed: D11.2 (A), U48.13 (Q2), U49.16 (B2)
unnamed: D12.1 (K), R21.1
unnamed: D12.2 (A), U48.12 (Q3), U49.15 (B3)
unnamed: D13.1 (K), R20.1
unnamed: D13.2 (A), U47.15 (Q0), U49.14 (B4)
unnamed: D14.1 (K), R19.1
unnamed: D14.2 (A), U47.14 (Q1), U49.13 (B5)
unnamed: D15.1 (K), R18.1
unnamed: D15.2 (A), U47.13 (Q2), U49.12 (B6)
unnamed: D16.1 (K), R17.1
unnamed: D16.2 (A), U47.12 (Q3), U49.11 (B7)
unnamed: R184.2, R185.2, U45.10 (CP), U46.10 (CP), U47.10 (CP), U48.10 (CP)
RI_0: U46.4 (P0)
RI_1: U46.5 (P1)
RI_2: U46.6 (P2)
RI_3: U46.7 (P3)
RI_4: U45.4 (P0)
RI_5: U45.5 (P1)
RI_6: U45.6 (P2)
RI_7: U45.7 (P3)
